mrrosoff/Forager/assets/source_photos/animals/banana_slug.jpg

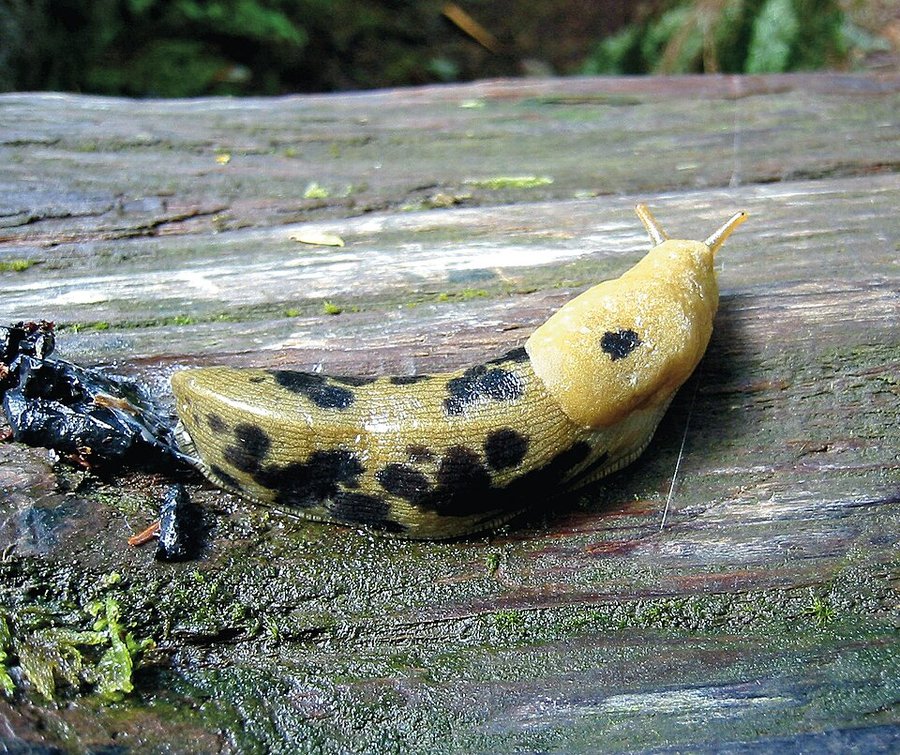
assets/source_photos/animals/banana_slug.jpg
