mrrosoff/Forager/assets/source_photos/animals/barred_owl.jpg

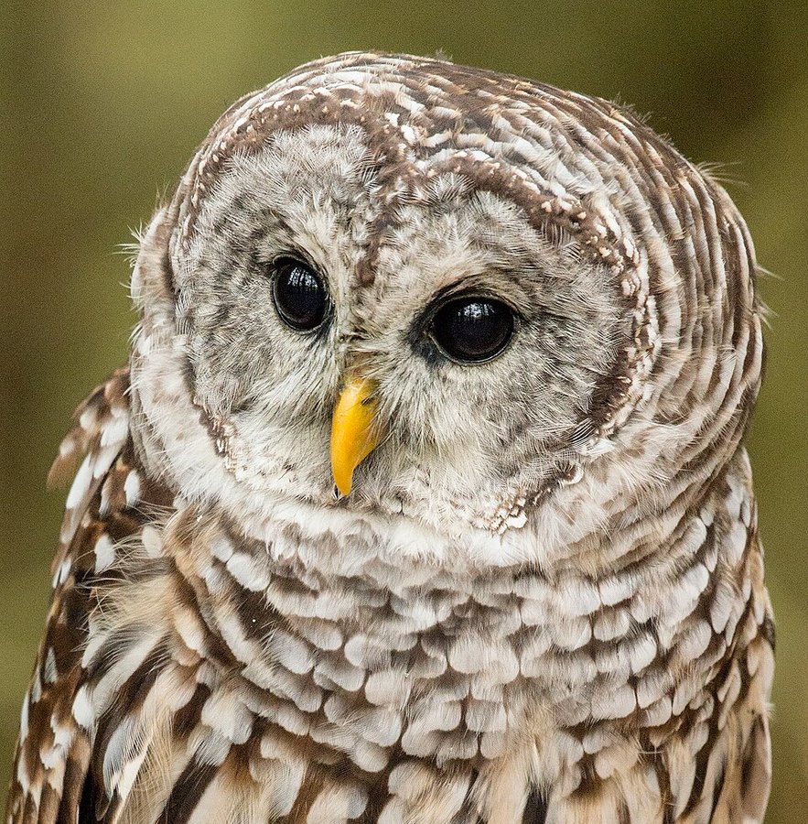
assets/source_photos/animals/barred_owl.jpg
