mrrosoff/Forager/assets/source_photos/animals/beaver.jpg

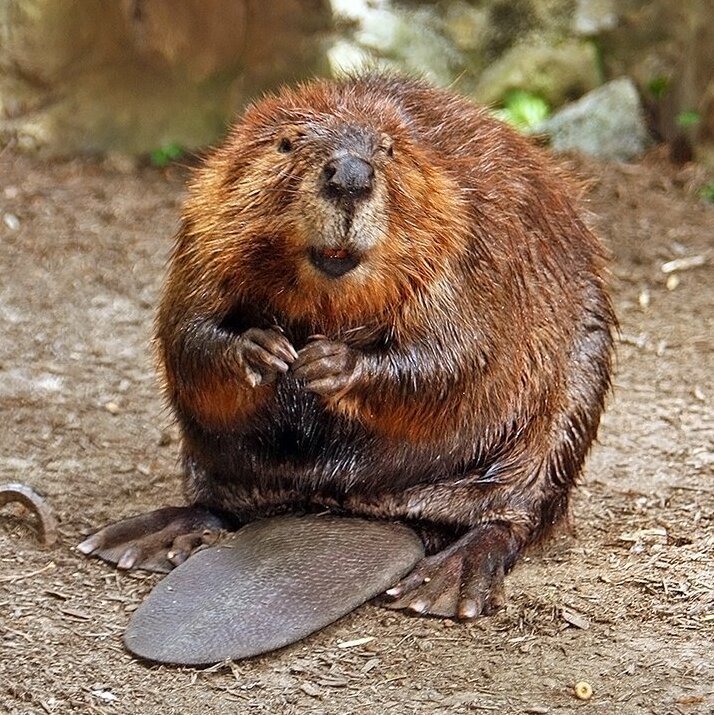
assets/source_photos/animals/beaver.jpg
