mrrosoff/Forager/assets/source_photos/animals/black_bear.jpg

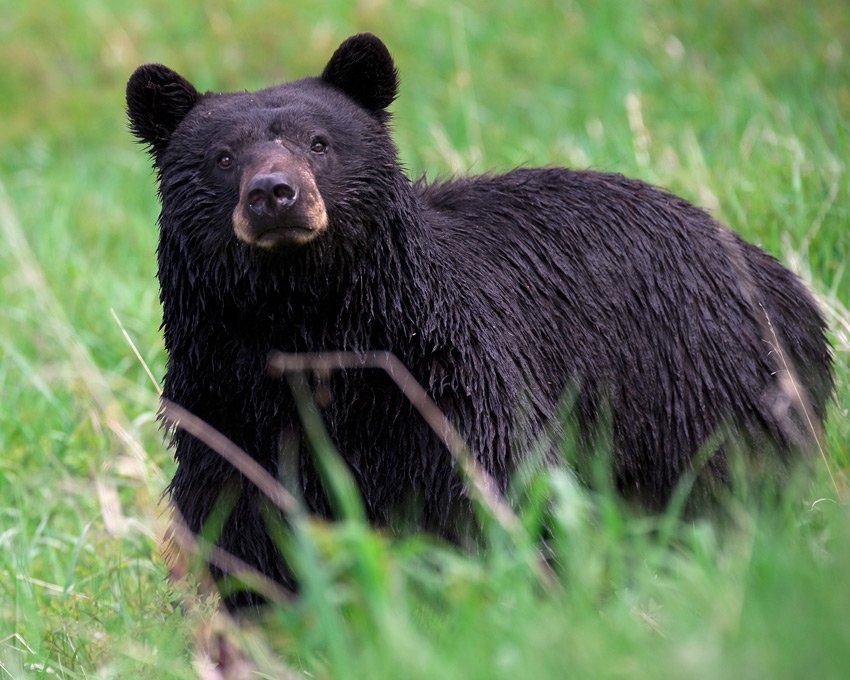
assets/source_photos/animals/black_bear.jpg
