mrrosoff/Forager/assets/source_photos/animals/bobcat.jpg

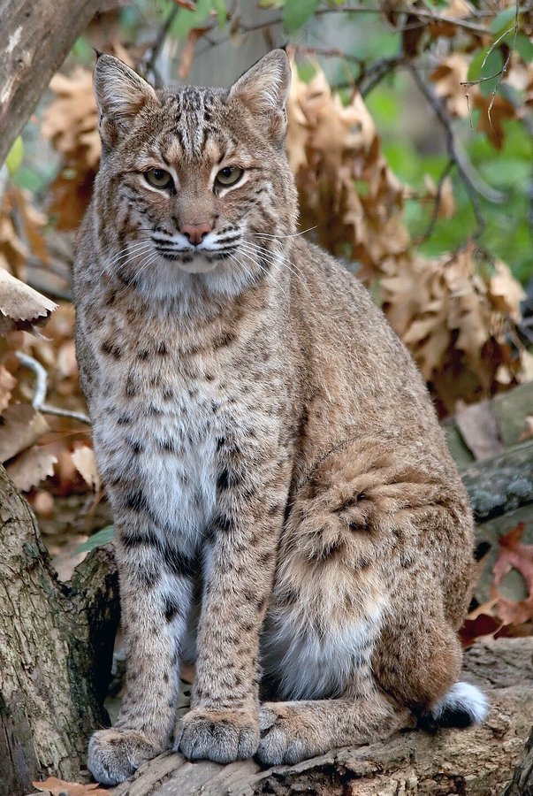
assets/source_photos/animals/bobcat.jpg
