mrrosoff/Forager/assets/source_photos/animals/chickadee.jpg

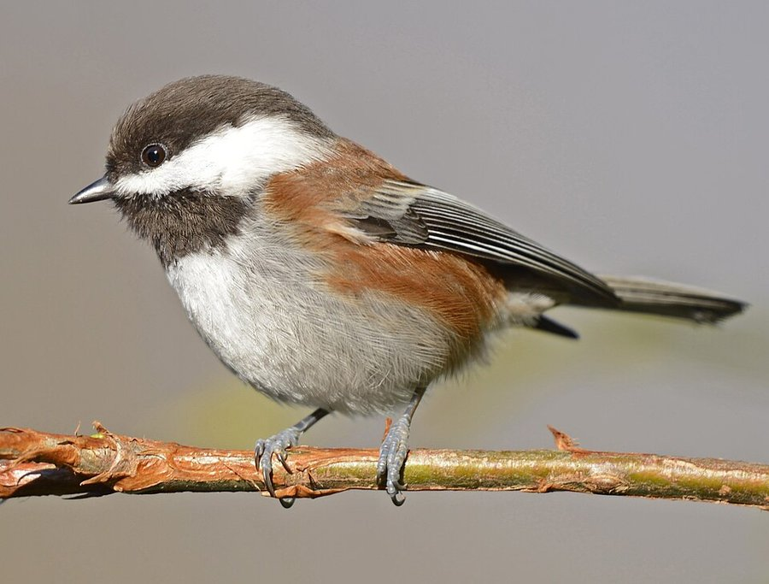
assets/source_photos/animals/chickadee.jpg
