mrrosoff/Forager/assets/source_photos/animals/cougar.jpg

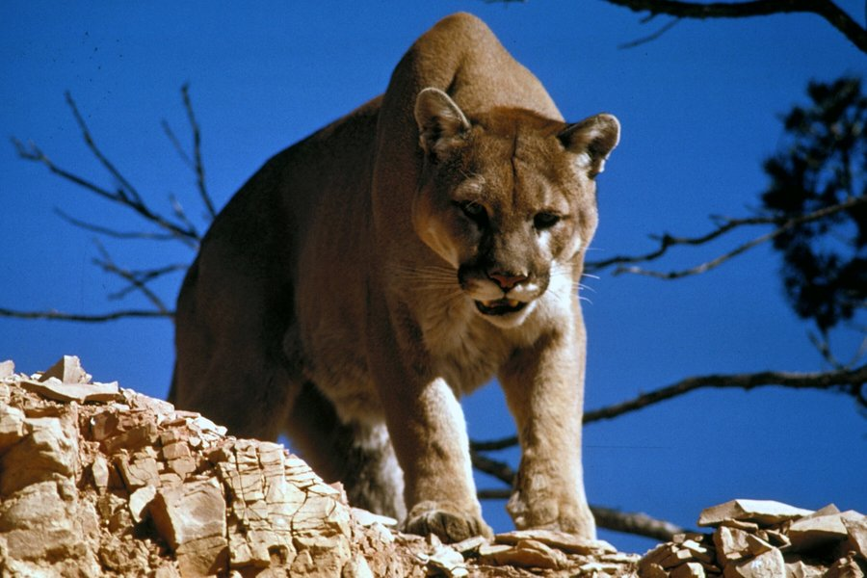
assets/source_photos/animals/cougar.jpg
