mrrosoff/Forager/assets/source_photos/animals/coyote.jpg

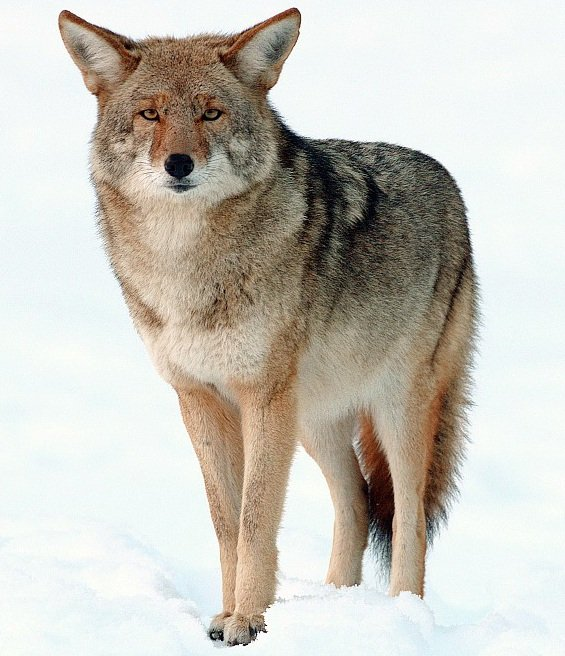
assets/source_photos/animals/coyote.jpg
