mrrosoff/Forager/assets/source_photos/animals/deer.jpg

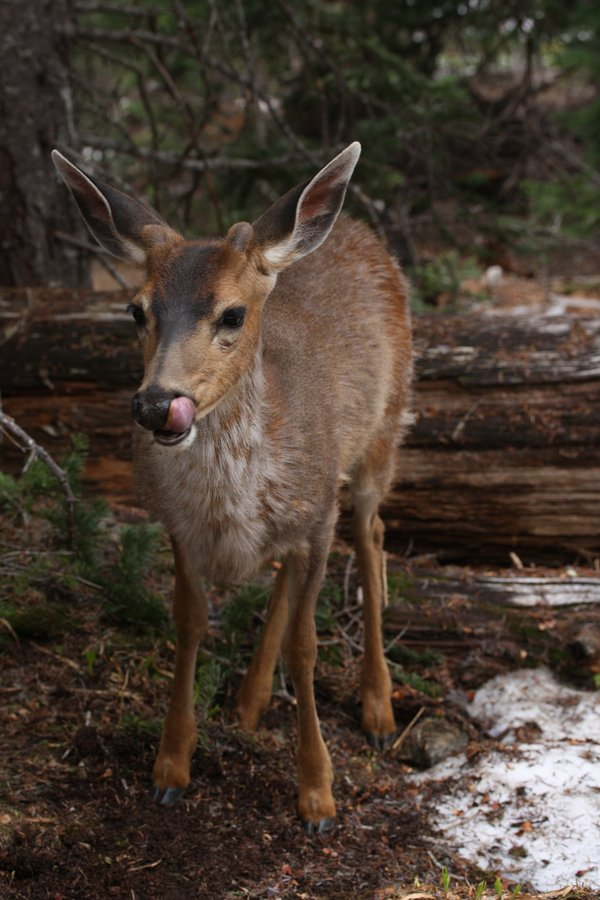
assets/source_photos/animals/deer.jpg
