mrrosoff/Forager/assets/source_photos/animals/elk.jpg

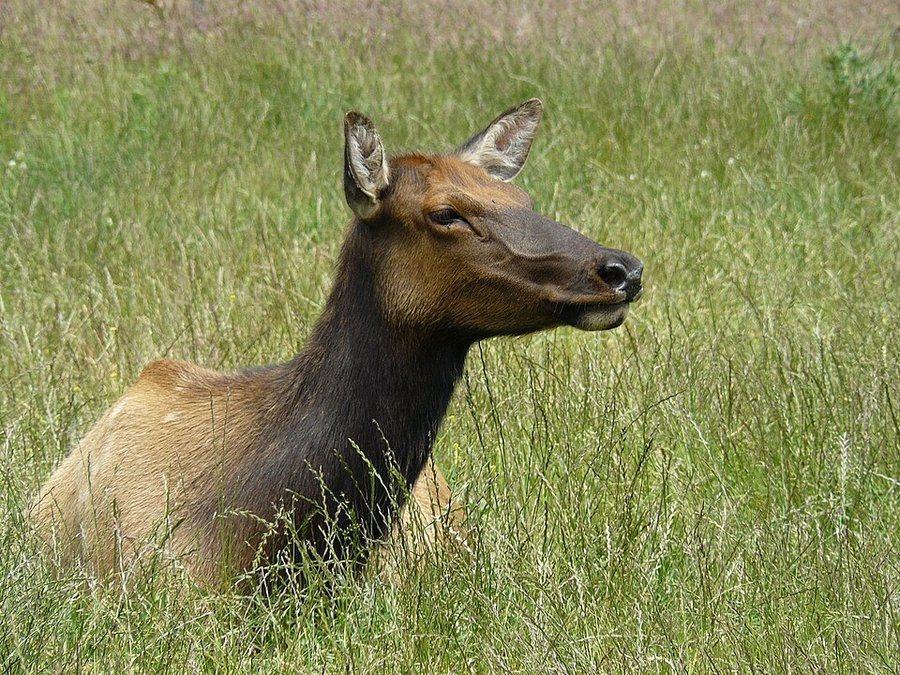
assets/source_photos/animals/elk.jpg
