mrrosoff/Forager/assets/source_photos/animals/gray_wolf.jpg

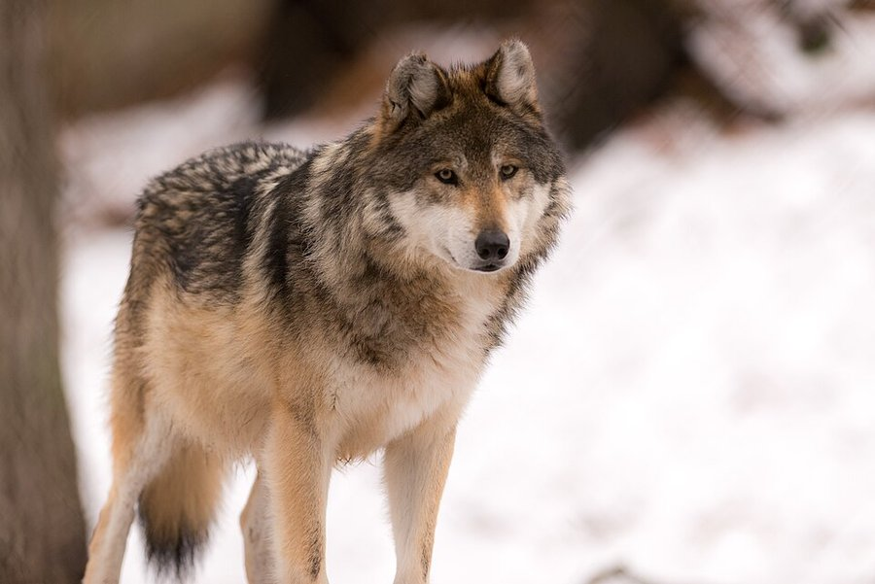
assets/source_photos/animals/gray_wolf.jpg
