mrrosoff/Forager/assets/source_photos/animals/great_blue_heron.jpg

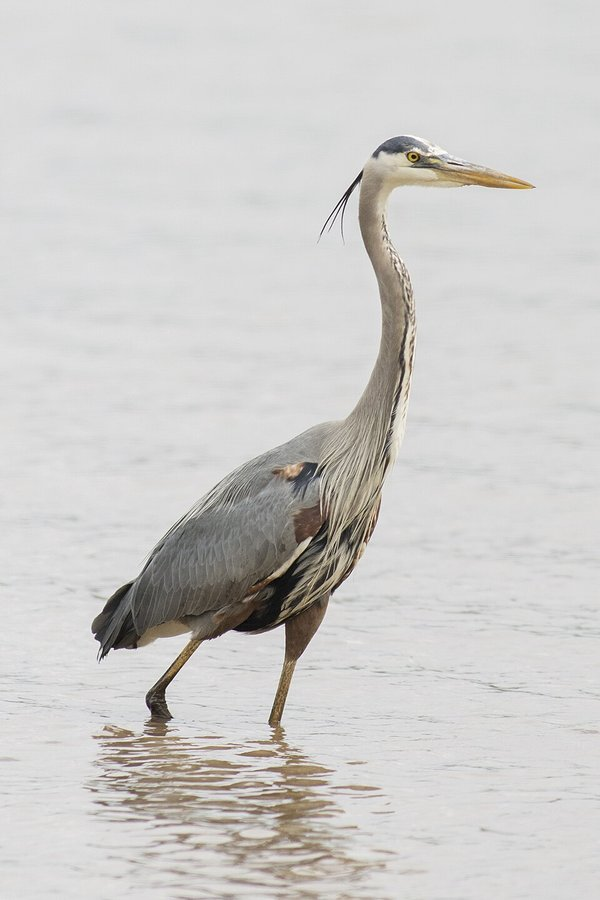
assets/source_photos/animals/great_blue_heron.jpg
