mrrosoff/Forager/assets/source_photos/animals/harbor_seal.jpg

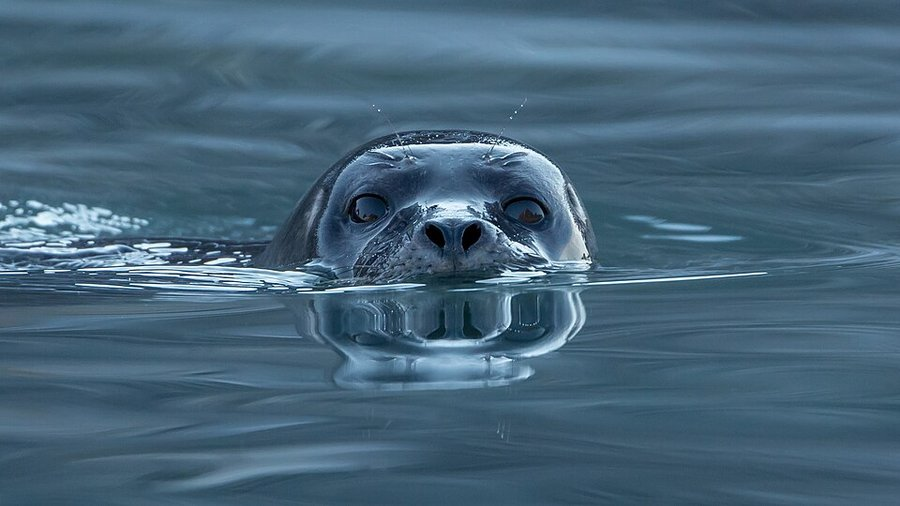
assets/source_photos/animals/harbor_seal.jpg
