mrrosoff/Forager/assets/source_photos/animals/mountain_goat.jpg

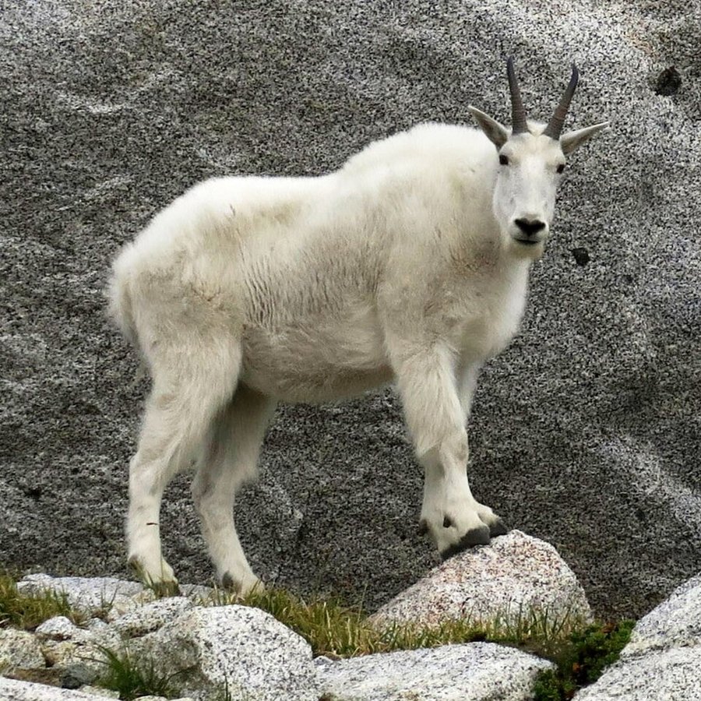
assets/source_photos/animals/mountain_goat.jpg
