mrrosoff/Forager/assets/source_photos/animals/orca.jpg

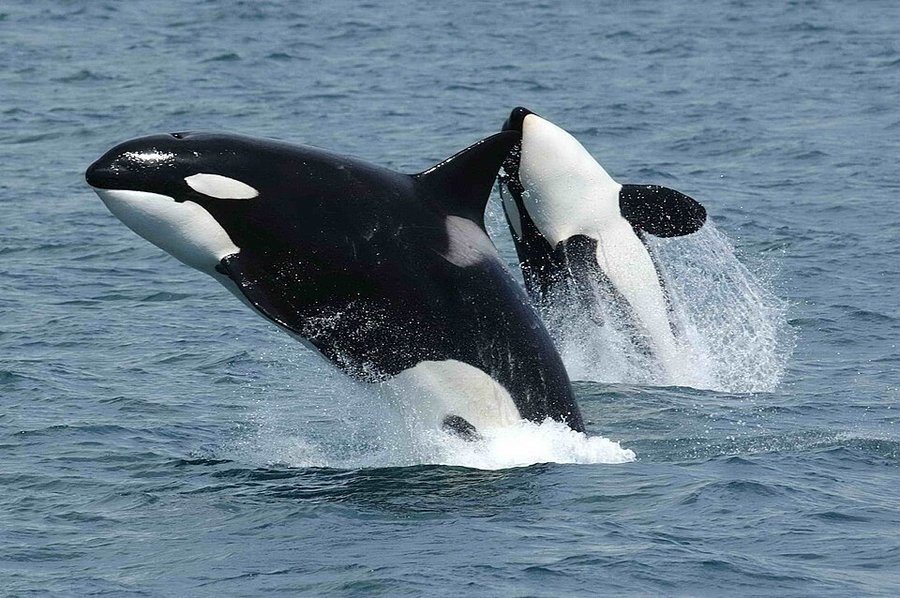
assets/source_photos/animals/orca.jpg
