mrrosoff/Forager/assets/source_photos/animals/osprey.jpg

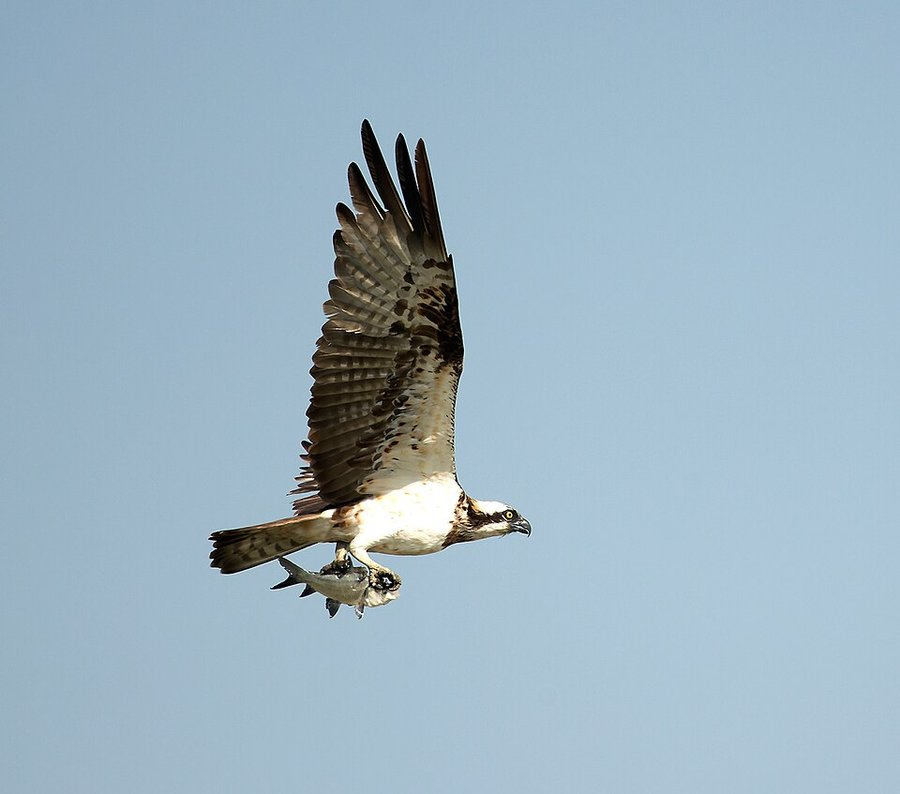
assets/source_photos/animals/osprey.jpg
