mrrosoff/Forager/assets/source_photos/animals/pacific_tree_frog.jpg

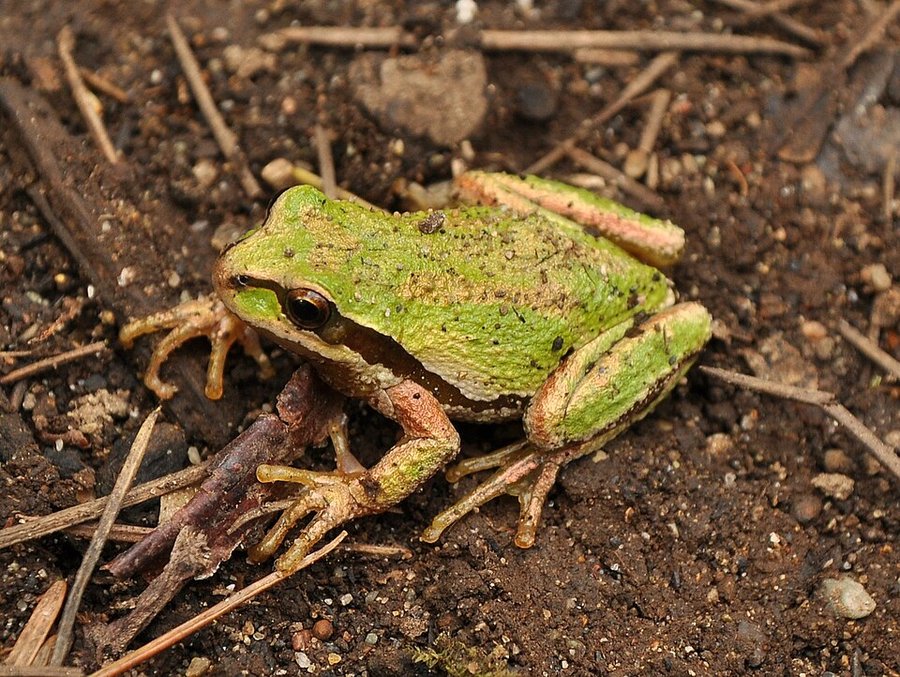
assets/source_photos/animals/pacific_tree_frog.jpg
