mrrosoff/Forager/assets/source_photos/animals/pileated_woodpecker.jpg

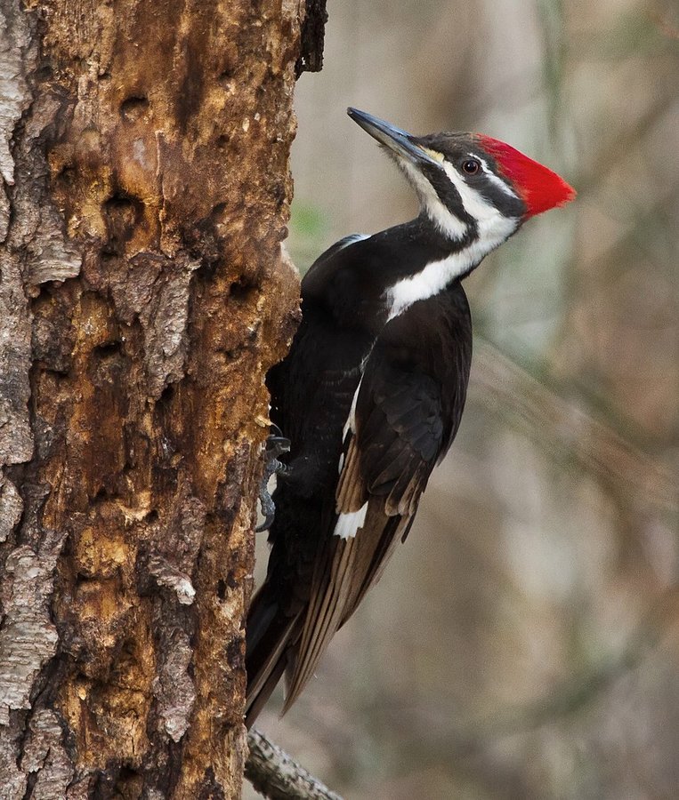
assets/source_photos/animals/pileated_woodpecker.jpg
