mrrosoff/Forager/assets/source_photos/animals/red_fox.jpg

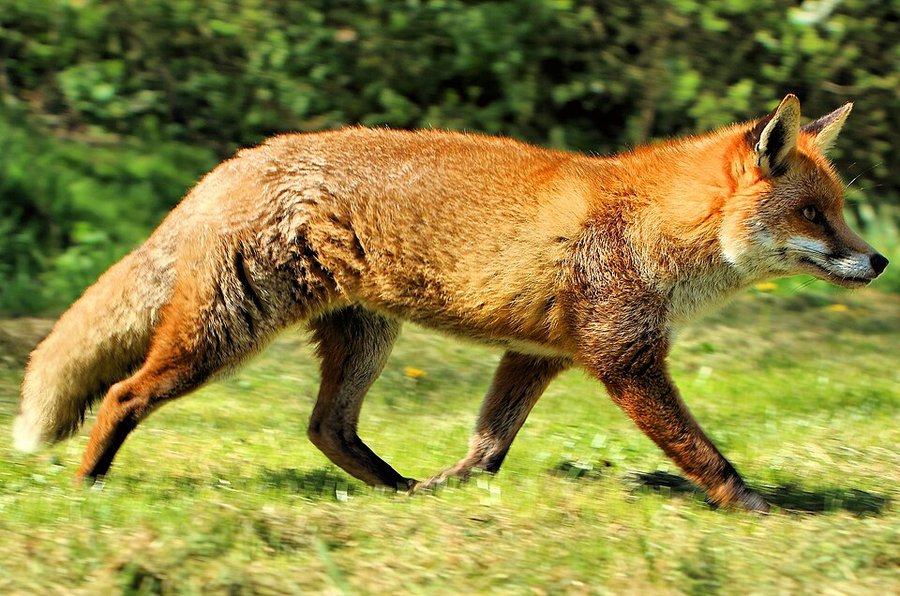
assets/source_photos/animals/red_fox.jpg
