mrrosoff/Forager/assets/source_photos/animals/river_otter.jpg

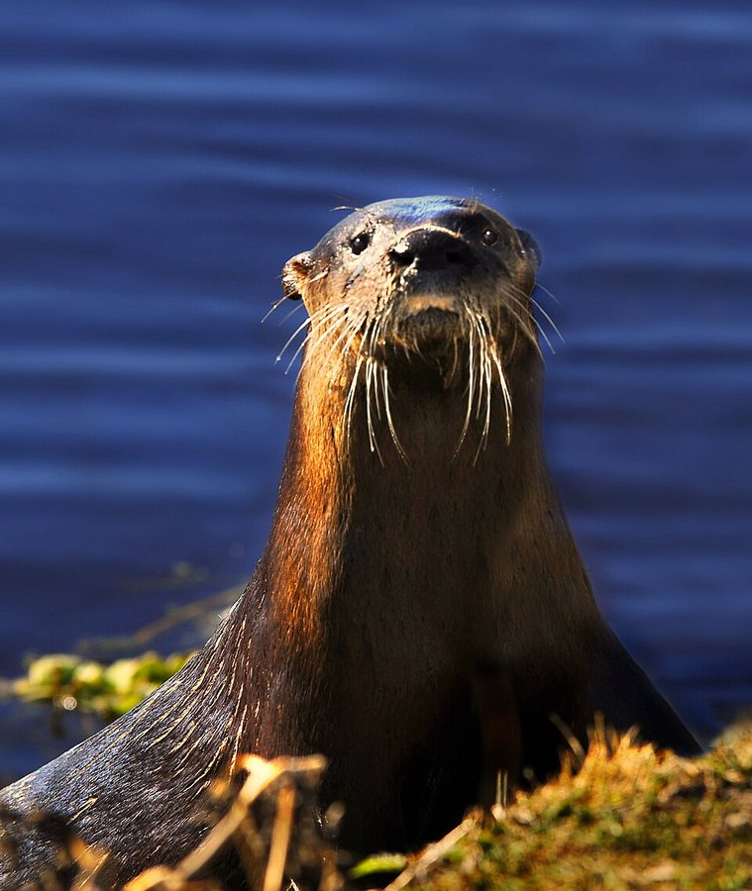
assets/source_photos/animals/river_otter.jpg
