mrrosoff/Forager/assets/source_photos/animals/snowshoe_hare.jpg

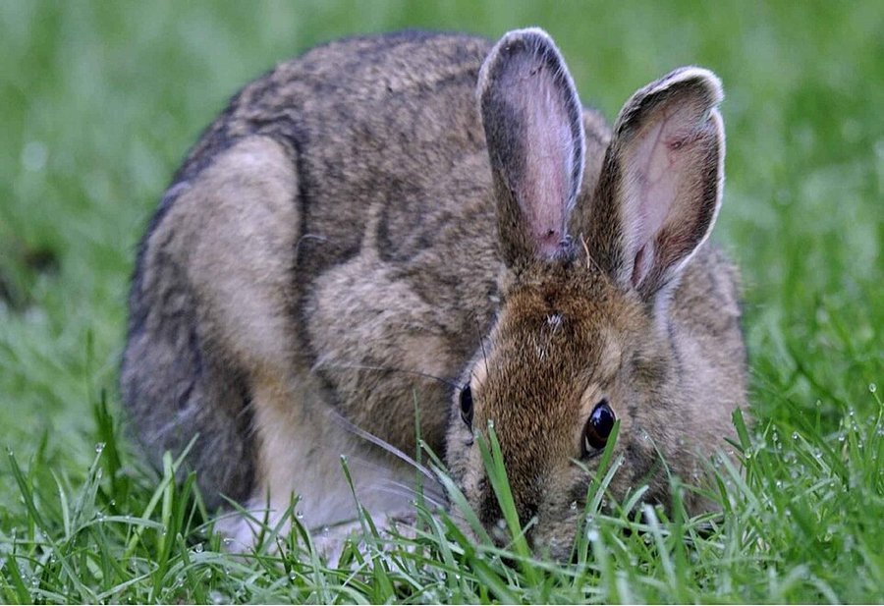
assets/source_photos/animals/snowshoe_hare.jpg
