mrrosoff/Forager/assets/source_photos/animals/stellers_jay.jpg

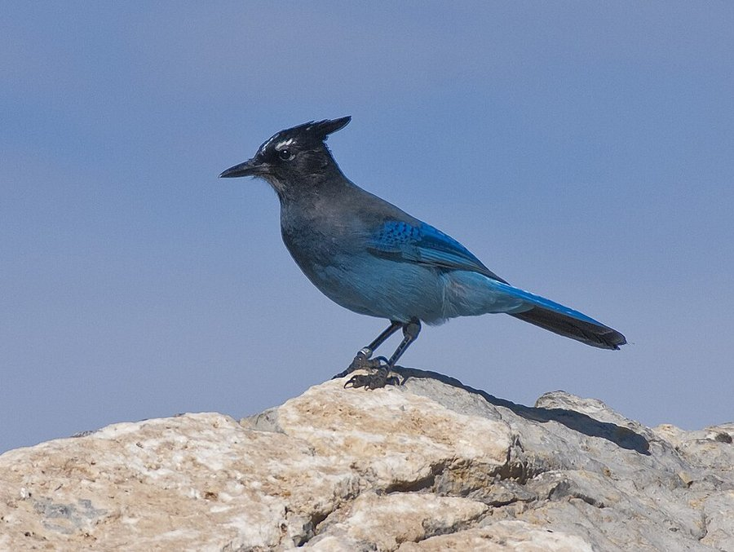
assets/source_photos/animals/stellers_jay.jpg
