mrrosoff/Forager/assets/source_photos/marmot/baby2.jpg

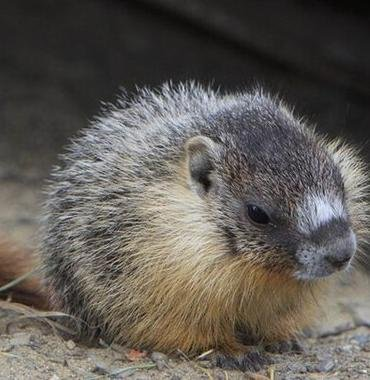
assets/source_photos/marmot/baby2.jpg
