mrrosoff/Forager/assets/source_photos/marmot/baby4.jpg

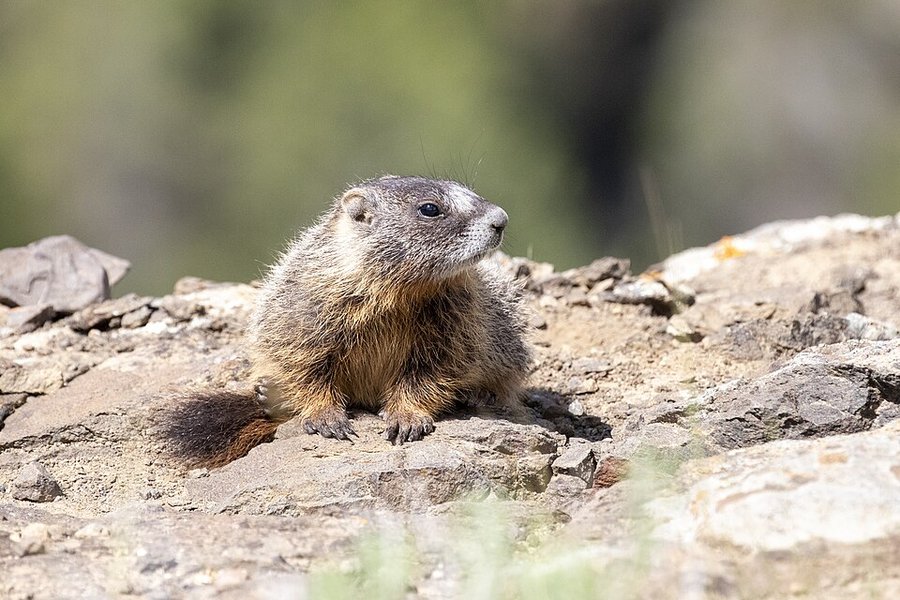
assets/source_photos/marmot/baby4.jpg
