mrrosoff/Forager/assets/source_photos/marmot/baby6.jpg

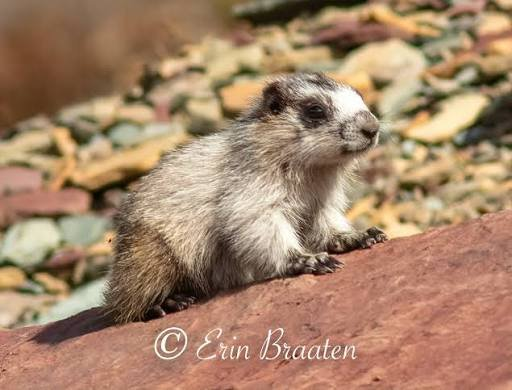
assets/source_photos/marmot/baby6.jpg
