mrrosoff/Forager/assets/source_photos/marmot/baby7.jpg

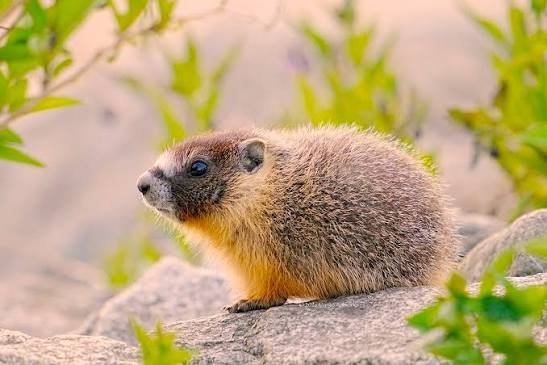
assets/source_photos/marmot/baby7.jpg
