mrrosoff/Forager/assets/source_photos/marmot/baby.jpg

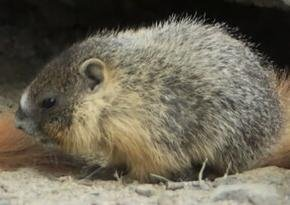
assets/source_photos/marmot/baby.jpg
