mrrosoff/Forager/assets/source_photos/marmot/base.jpg

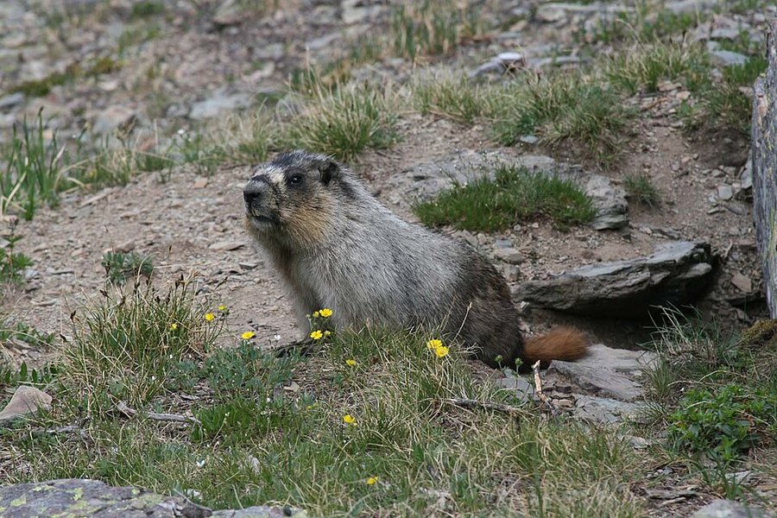
assets/source_photos/marmot/base.jpg
