mrrosoff/Forager/assets/source_photos/marmot/death.jpg

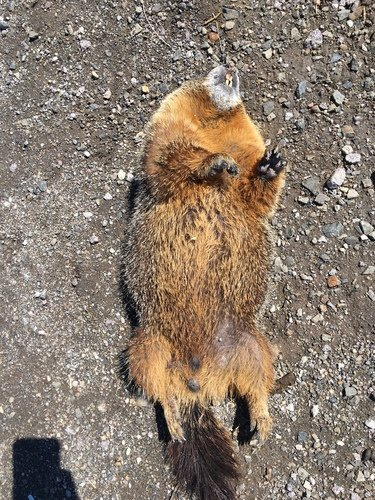
assets/source_photos/marmot/death.jpg
