mrrosoff/Forager/assets/source_photos/marmot/variant5.jpg

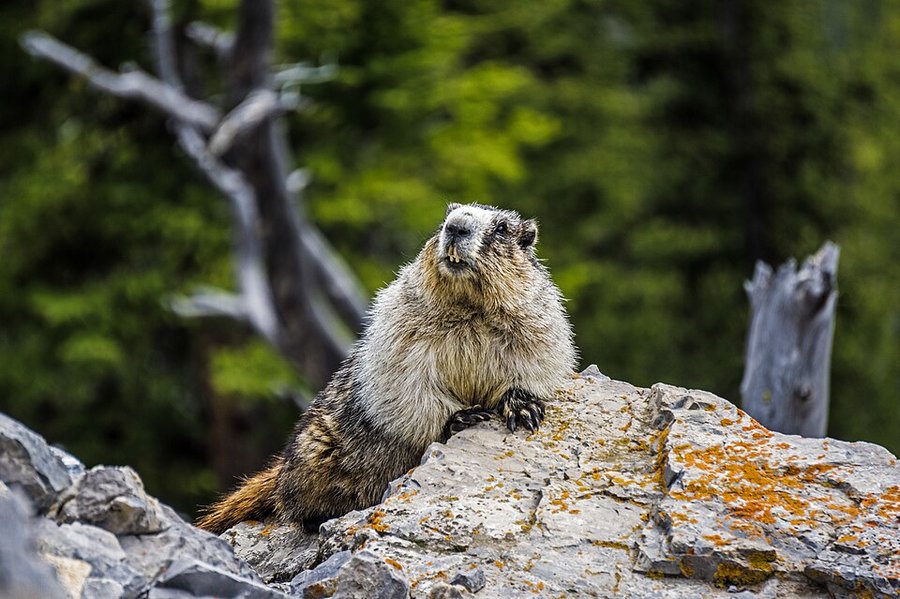
assets/source_photos/marmot/variant5.jpg
