mrrosoff/Forager/assets/source_photos/marmot/variant6.jpg

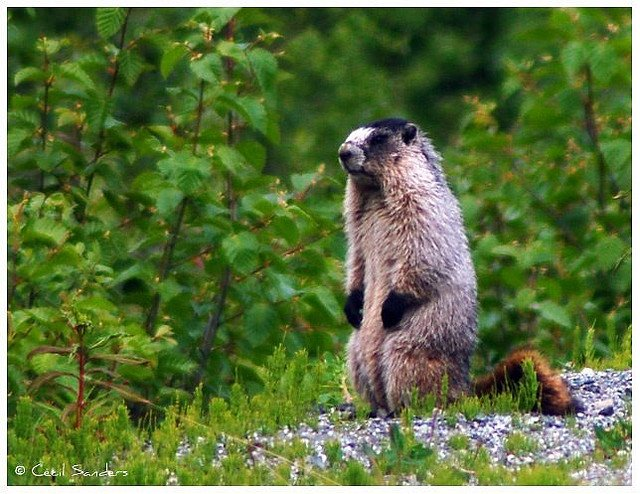
assets/source_photos/marmot/variant6.jpg
