mrrosoff/Forager/assets/source_photos/marmot/variant7.jpg

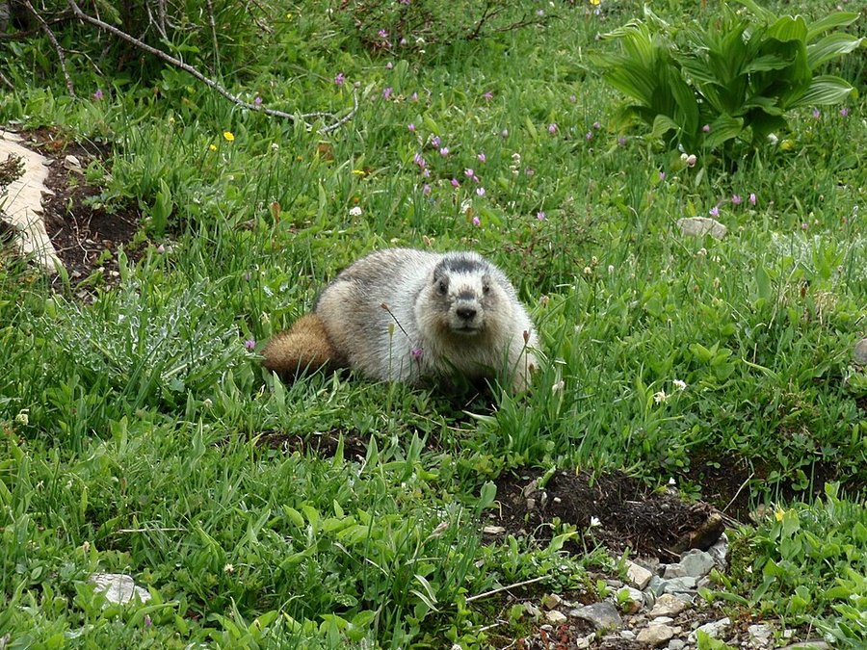
assets/source_photos/marmot/variant7.jpg
