mrrosoff/Forager/assets/source_photos/marmot/variant8.jpg

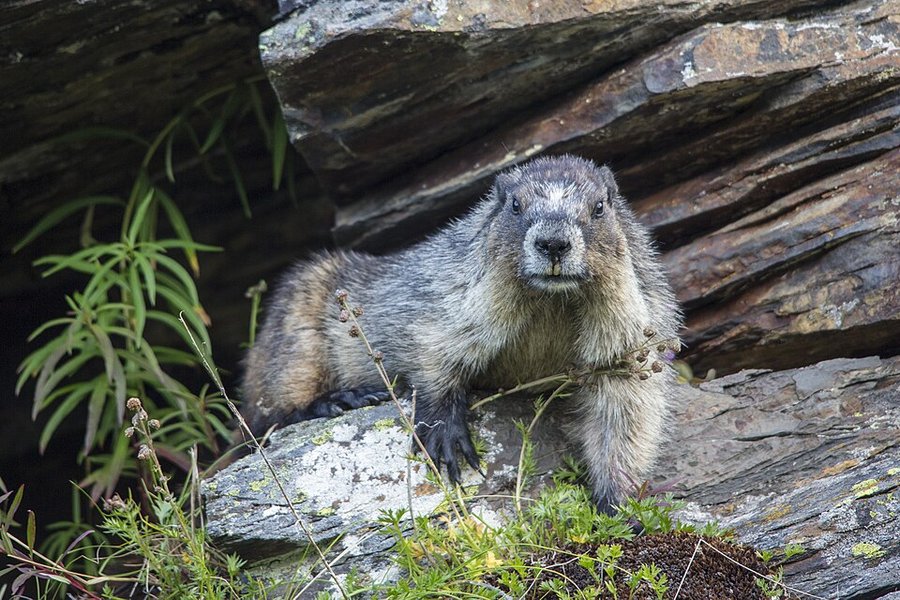
assets/source_photos/marmot/variant8.jpg
