mrrosoff/Forager/assets/source_photos/marmot/variant9.jpg

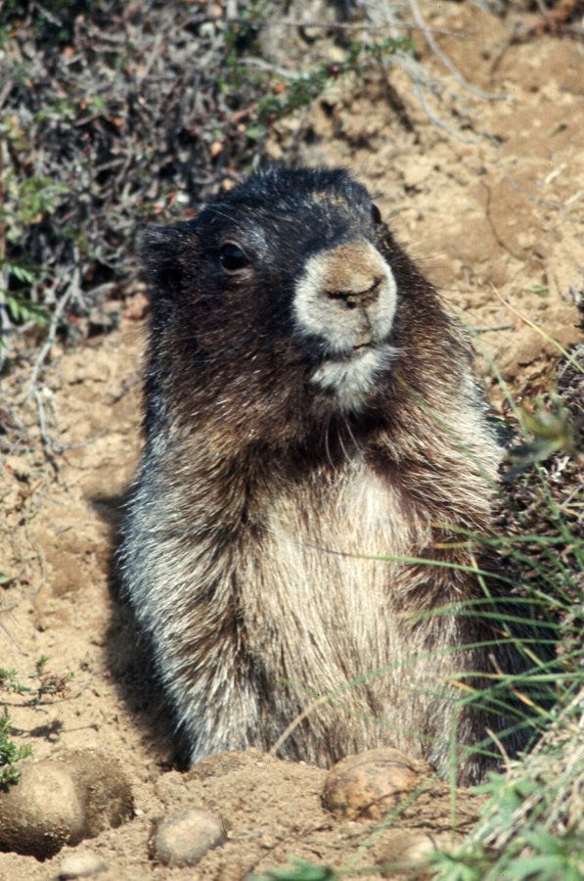
assets/source_photos/marmot/variant9.jpg
