mrrosoff/Forager/assets/source_photos/marmot/variant10.jpg

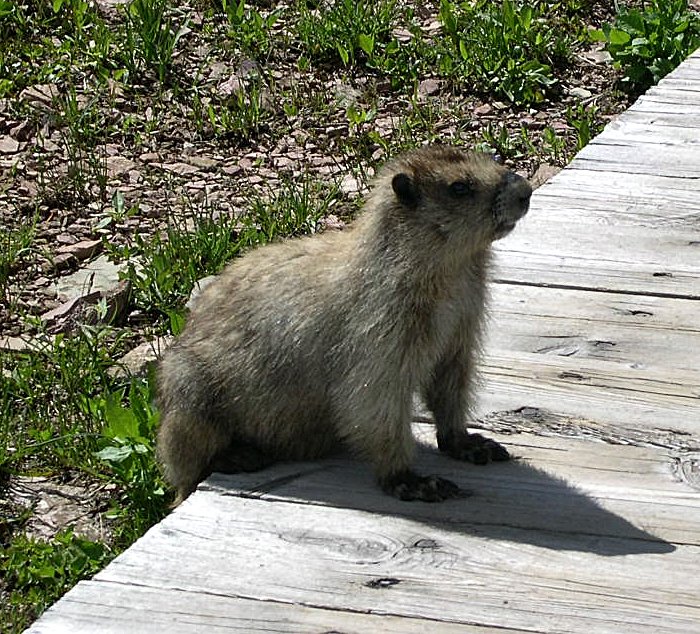
assets/source_photos/marmot/variant10.jpg
