mrrosoff/Forager/assets/source_photos/marmot/variant11.jpg

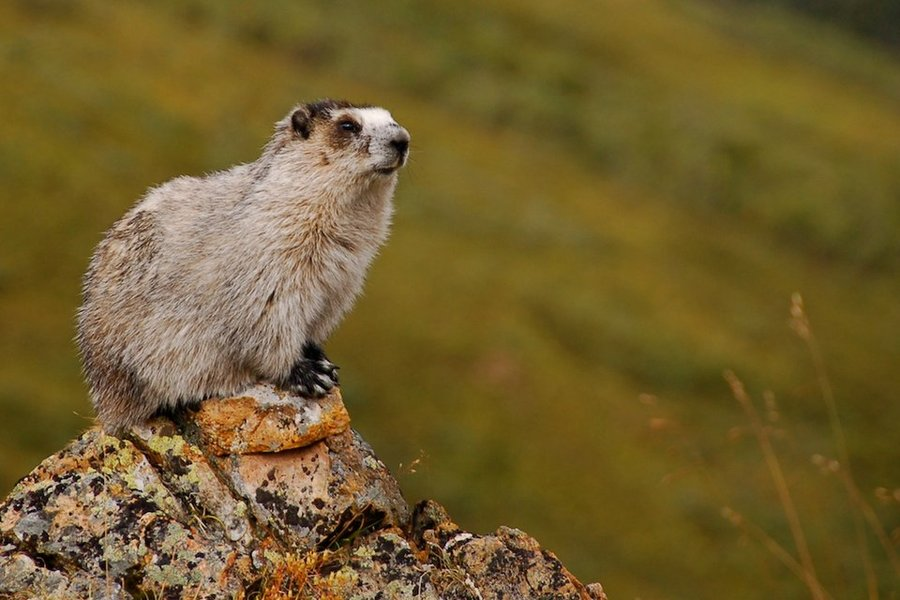
assets/source_photos/marmot/variant11.jpg
