mrrosoff/Forager/assets/source_photos/marmot/variant16.jpg

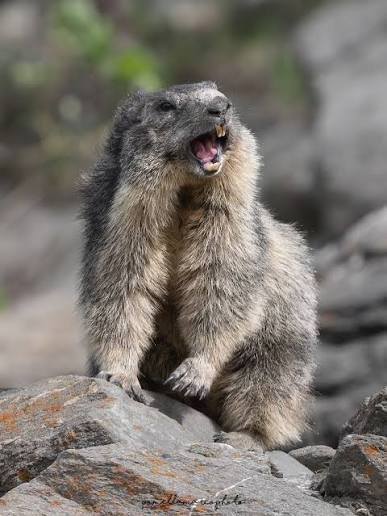
assets/source_photos/marmot/variant16.jpg
