mrrosoff/Forager/assets/source_photos/marmot/variant17.jpg

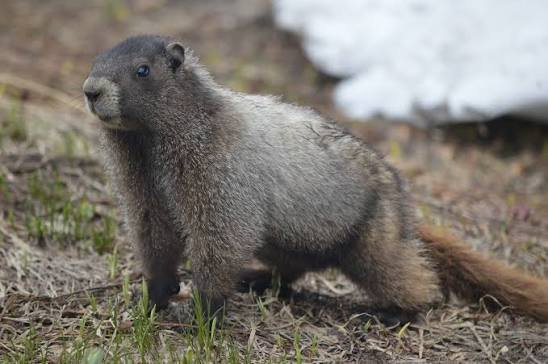
assets/source_photos/marmot/variant17.jpg
