mrrosoff/Forager/assets/source_photos/marmot/variant18.jpg

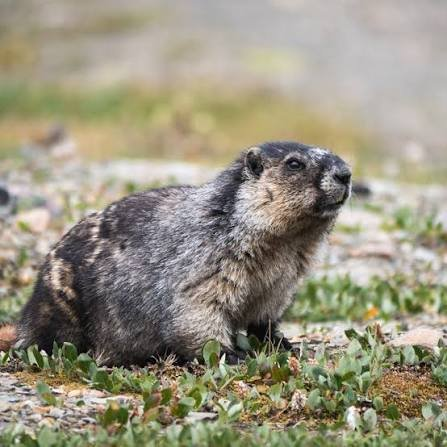
assets/source_photos/marmot/variant18.jpg
