mrrosoff/Forager/assets/source_photos/marmot/variant20.jpg

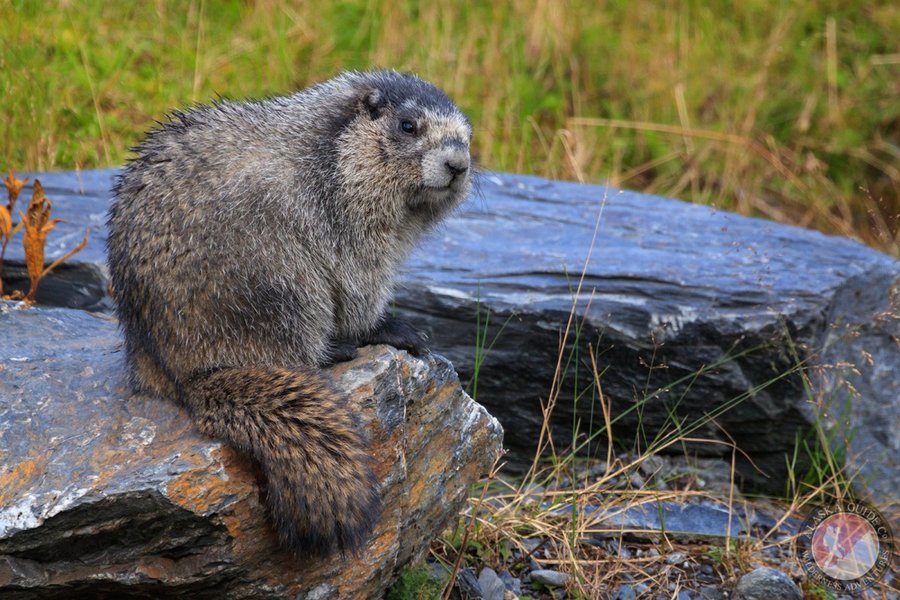
assets/source_photos/marmot/variant20.jpg
