mrrosoff/Forager/assets/source_photos/marmot/variant21.jpg

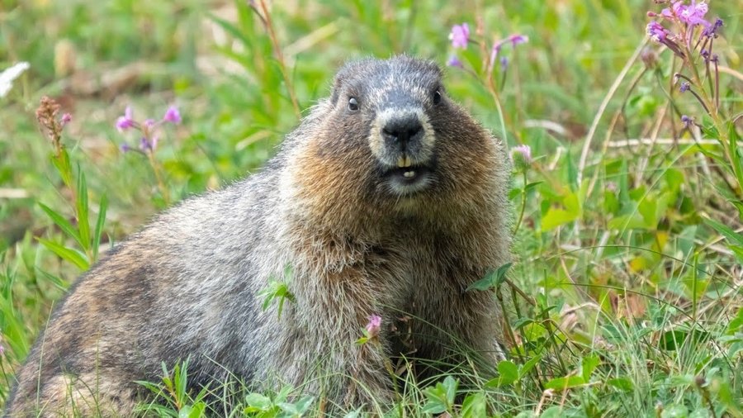
assets/source_photos/marmot/variant21.jpg
