mrrosoff/Forager/assets/source_photos/marmot/variant22.jpg

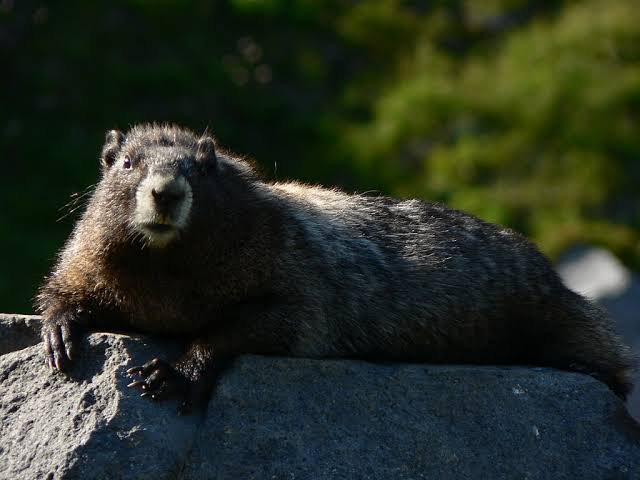
assets/source_photos/marmot/variant22.jpg
