mrrosoff/Forager/assets/source_photos/marmot/variant24.jpg

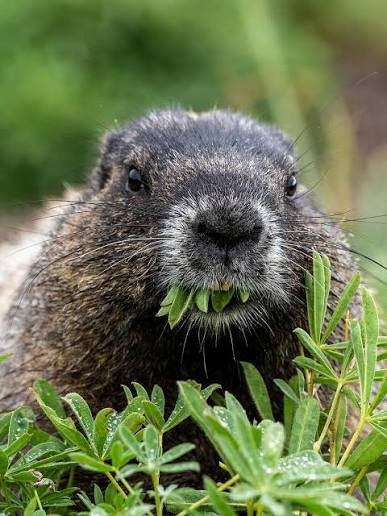
assets/source_photos/marmot/variant24.jpg
