mrrosoff/Forager/assets/source_photos/marmot/variant25.jpg

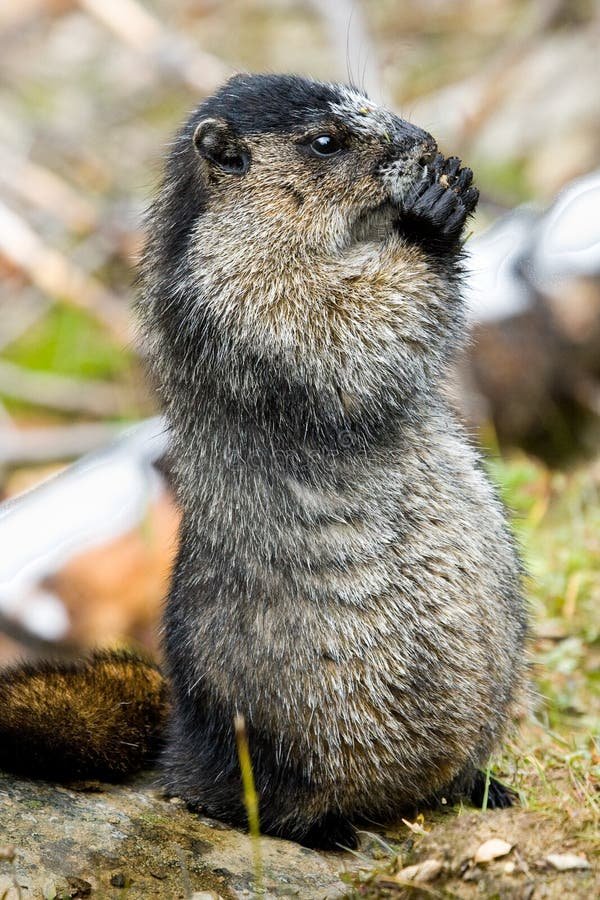
assets/source_photos/marmot/variant25.jpg
