mrrosoff/Forager/assets/source_photos/marmot/variant26.jpg

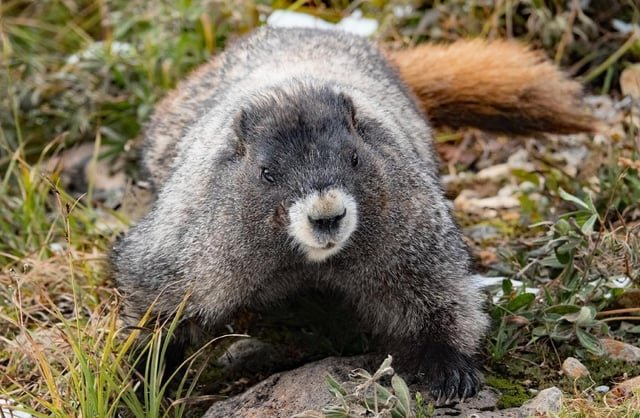
assets/source_photos/marmot/variant26.jpg
