mrrosoff/Forager/assets/source_photos/marmot/variant27.jpg

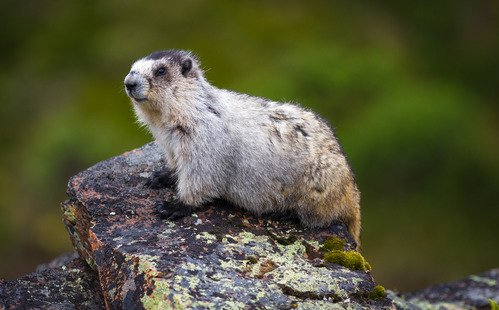
assets/source_photos/marmot/variant27.jpg
