mrrosoff/Forager/assets/source_photos/marmot/variant28.jpg

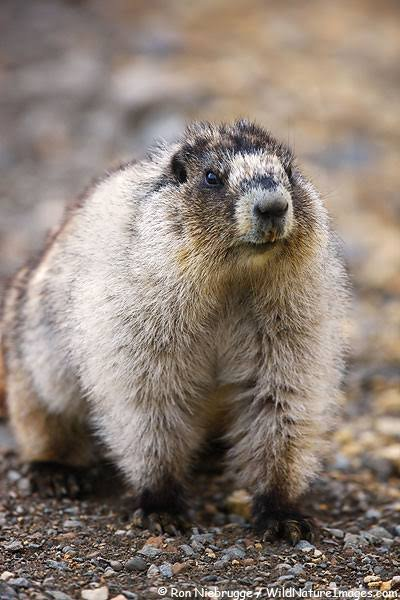
assets/source_photos/marmot/variant28.jpg
