mrrosoff/Forager/enclosure/preview/01_bezel_front.png

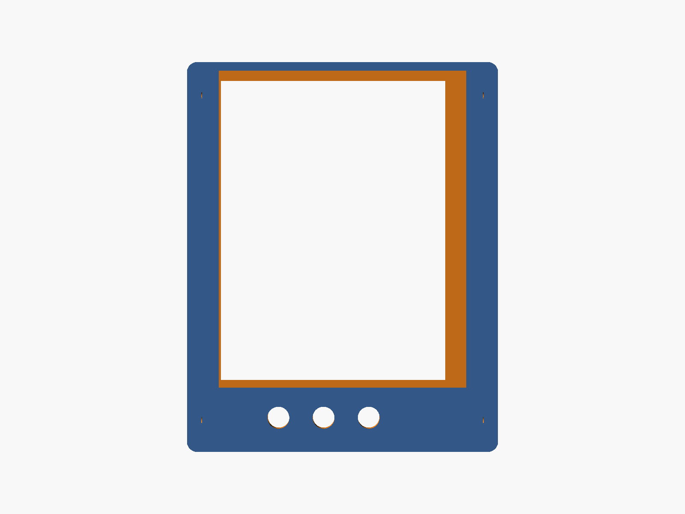
enclosure/preview/01_bezel_front.png
