mrrosoff/Forager/enclosure/preview/02_bezel_iso.png

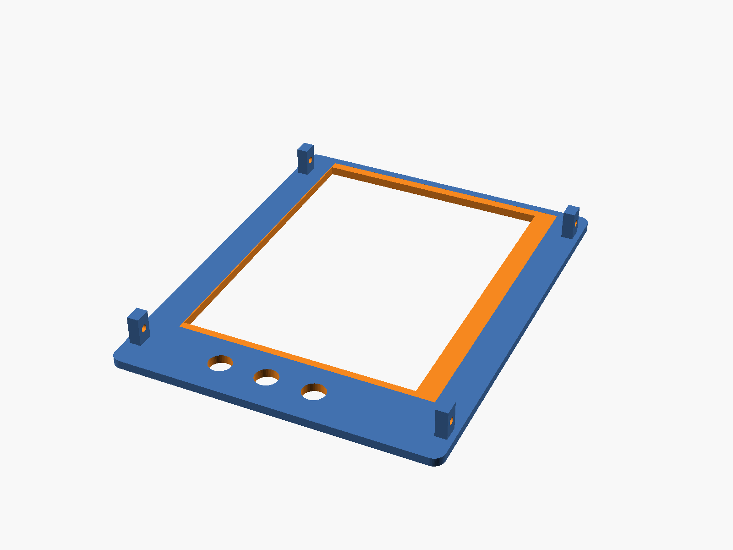
enclosure/preview/02_bezel_iso.png
