mrrosoff/Forager/enclosure/preview/03_tray_interior.png

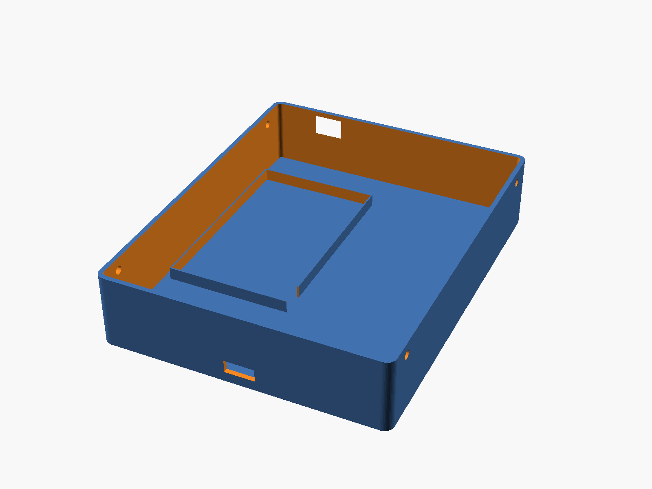
enclosure/preview/03_tray_interior.png
