mrrosoff/Forager/enclosure/preview/04_tray_exterior.png

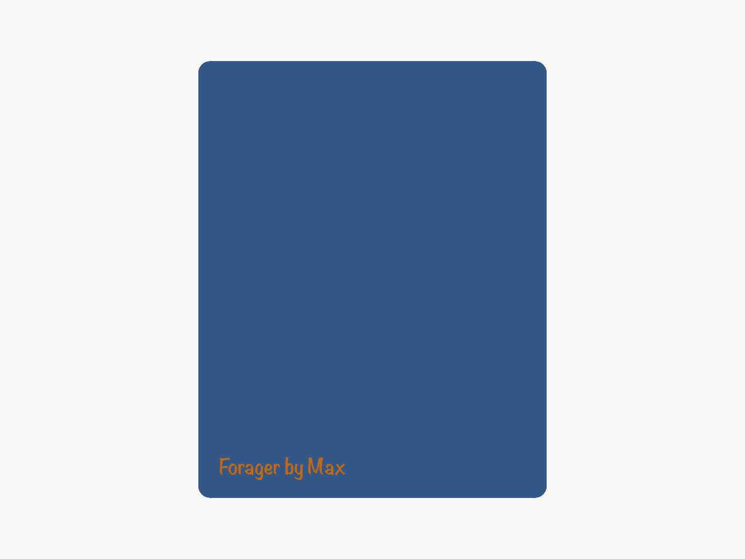
enclosure/preview/04_tray_exterior.png
