mrrosoff/Forager/enclosure/preview/05_assembled_overview.png

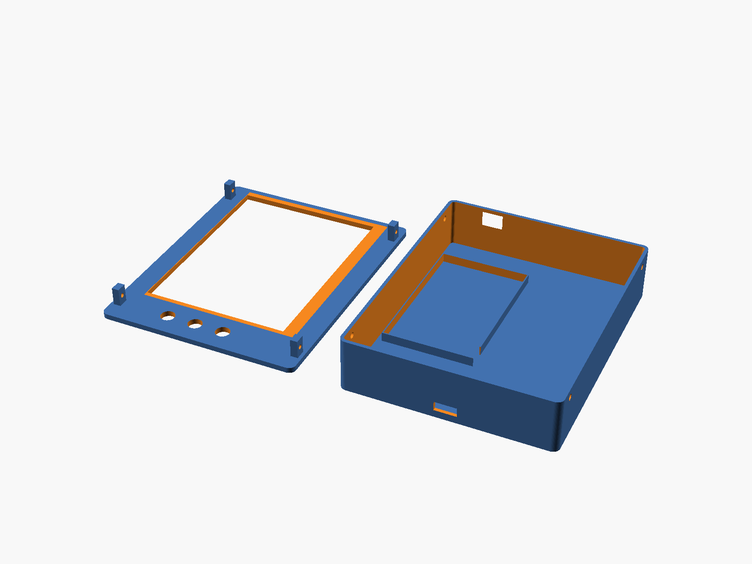
enclosure/preview/05_assembled_overview.png
