mrrosoff/Forager/src/foraging/foraging_species.h

// foraging_species.h — the master PNW/Seattle foraging reference table.
// Pure data, split out of foraging.cpp so that file is mostly logic. Only
// included from foraging.cpp, which #defines the MO(month) bitmask macro
// used throughout before including this.
#pragma once

#include "model.h"

// monthMask bits mark active months (1=Jan .. 12=Dec, via the MO() macro).
// caution is "" when there's no meaningful look-alike risk.
static const Forageable kSpecies[] = {
    {"Dead Man's Fingers", "mushroom", "Dark charcoal-black finger-like clubs pushing up from buried wood.",
     "Not edible -- tough and bitter, just a striking find.",
     "Look for the dark clustered fingers at the base of rotting stumps.", MO(6) | MO(7) | MO(8),
     Biome::Forest},

    {"Miner's Lettuce", "green", "Round leaf cupping the stem. Shady wet banks.", "",
     "Snip above the root so the patch regrows.", MO(1) | MO(2) | MO(3), Biome::Forest},

    {"Stinging Nettle", "green", "First tips now. Gloves on; cooking kills the sting.",
     "Wear gloves -- fresh leaves sting on contact.",
     "Pick only the top 4-6 leaves per plant, gloved.", MO(2) | MO(3) | MO(4), Biome::Forest},

    {"Oyster Mushroom", "mushroom", "Shelving on dead alder and maple after rain.",
     "Check for the Angel Wing lookalike on conifers -- avoid it.",
     "Cut at the base of the cluster, leave small ones.", MO(1) | MO(2) | MO(11) | MO(12),
     Biome::Forest},

    {"Morel", "mushroom", "Honeycomb cap. Watch cottonwoods as soil warms.",
     "True morels are hollow top to bottom -- cut one to confirm.",
     "Check burn sites and cottonwood river bottoms.", MO(3) | MO(4), Biome::Forest},

    {"Chickweed", "green", "Tender mats in disturbed ground. Mild, fresh.", "",
     "Best before flowering; snip the top few inches.", MO(3) | MO(4) | MO(5), Biome::Forest},

    {"Ramps", "green", "Wild leek. Harvest one leaf, leave the bulb.", "",
     "Take a single leaf per plant so the patch survives.", MO(4), Biome::Forest},

    {"Fiddlehead Fern", "green", "Tight coils of lady fern. Pick before they unfurl.",
     "Must be cooked thoroughly; avoid bracken fern lookalikes.",
     "Snap coils that are still tightly curled, under 2 inches.", MO(4) | MO(5), Biome::Forest},

    {"Elderflower", "flower", "Creamy umbels. Cordial weather. Never the leaves.",
     "Leaves and stems are toxic -- flowers and ripe berries only.",
     "Cut whole flower clusters, shake off insects first.", MO(5) | MO(6), Biome::Forest},

    {"Wood Sorrel", "green", "Shamrock leaf, lemony bite. Forest floor and trailside.",
     "High in oxalic acid -- a trailside nibble, not a meal.",
     "Pinch leaves and stems; avoid roadside patches.", MO(5) | MO(6) | MO(7), Biome::Forest},

    {"Salmonberry", "berry", "Earliest berry. Golden to red, along streams.", "",
     "Ripe berries pull free easily; unripe ones resist.", MO(6), Biome::Forest},

    {"Chanterelle", "mushroom", "Apricot scent, false gills. Conifer duff after warm rain.",
     "False ridges, not true blades -- a key ID feature vs toxic lookalikes.",
     "Look on slopes under Douglas fir a week after rain.", MO(7) | MO(8) | MO(9), Biome::Forest},

    {"Blackberry", "berry", "Himalayan brambles everywhere. Sun-warmed edges.", "",
     "Sun-facing berries ripen first; watch for thorns.", MO(8) | MO(9), Biome::Forest},

    {"Matsutake", "mushroom", "Spicy-cinnamon pine mushroom. Sandy conifer soil.", "",
     "Look for cracked duff mounds near pine roots.", MO(9), Biome::Forest},

    {"Lobster Mushroom", "mushroom", "Orange parasitized host. Firm, seafood-sweet.",
     "The host mushroom underneath is irrelevant once parasitized.",
     "Firm all the way through means it's good to eat.", MO(9) | MO(10), Biome::Forest},

    {"Porcini", "mushroom", "King bolete. Fat white stem, no gills -- pores instead.",
     "Check for pores, not gills; avoid soft or wormy caps.",
     "Firm caps only; check the stem base for grubs.", MO(10), Biome::Forest},

    {"Yellowfoot", "mushroom", "Winter chanterelle. Hollow stem, late and cold-hardy.", "",
     "Keeps fruiting through light frost -- check familiar patches.", MO(11) | MO(12),
     Biome::Forest},

    {"Velvet Shank", "mushroom", "Enokitake's wild cousin. Orange caps in cold snaps.",
     "Sticky cap and velvety stem distinguish it from toxic Galerina.",
     "Fruits on hardwood stumps during cold snaps.", MO(12) | MO(1), Biome::Forest},

    {"Huckleberry", "berry", "Subalpine slopes. Ripens as you gain elevation.", "",
     "Higher elevation = later ripening; chase the season uphill.", MO(7) | MO(8), Biome::Mountain},

    {"Raspberry", "berry", "Wild cane fruit at forest edges and old clearings.", "",
     "Tug ripe berries gently -- they pull free of the core when ready.", MO(7) | MO(8),
     Biome::Mountain},

    {"Mountain Cranberry", "berry", "Lingonberry cousin. Tart red berries in dwarf mats.", "",
     "Best after light frost sweetens the fruit; pick sparingly.", MO(9) | MO(10), Biome::Mountain},

    {"Devil's Club Shoots", "green", "Spring shoots, mild and green before the spines toughen.",
     "Cook thoroughly; handle mature stalks with gloves -- spiny.",
     "Snap shoots while still tender, before leaves fully open.", MO(4) | MO(5), Biome::Mountain},

    {"Swamp Onion", "green", "Wild mountain onion in wet subalpine meadows.", "",
     "Pull gently from soft mud; rinse the bulb at the creek.", MO(6) | MO(7), Biome::Mountain},

    {"Douglas Fir Tips", "flower", "Bright citrus-pine new growth at branch ends.",
     "Don't confuse with Pacific yew -- yew needles are toxic.",
     "Pinch only the pale new candle growth, not old needles.", MO(4) | MO(5), Biome::Mountain},

    {"Bull Kelp", "seaweed", "Long whip stipe with a bulb float; drifts up after storms.",
     "Harvest drift only, or cut blade above the holdfast to regrow.",
     "Gather fresh drift kelp on the tideline after a blow.", MO(6) | MO(7) | MO(8) | MO(9),
     Biome::Coast},

    {"Sugar Kelp", "seaweed", "Wavy golden-brown blade in the low intertidal.", "",
     "Cut blades an inch above the holdfast at a minus tide.", MO(5) | MO(6) | MO(7), Biome::Coast},

    {"Sea Lettuce", "seaweed", "Bright green, tissue-thin sheets on mid-tide rocks.",
     "Rinse well -- can harbor grit and small amphipods.",
     "Pick loose, undamaged sheets; avoid ones near outfalls.", MO(4) | MO(5) | MO(6) | MO(7),
     Biome::Coast},

    {"Ochre Sea Star", "shellfish", "Chunky five-armed sea star in orange or deep purple, gripping rocks.",
     "Not edible -- a tidepool sight, not a snack.",
     "Look on rocky shores at low tide, often in tight clusters.", MO(6) | MO(7) | MO(8),
     Biome::Coast},

    {"Sea Asparagus", "green", "Pickleweed. Crunchy, salty segmented stems in the marsh.", "",
     "Snip the top two joints only, leave the rooted base.", MO(6) | MO(7) | MO(8) | MO(9),
     Biome::Coast},

    {"Goosetongue", "green", "Sea plantain. Fleshy, briny blades on the upper beach.", "",
     "Pick young center leaves; avoid grazed or muddy patches.", MO(5) | MO(6) | MO(7),
     Biome::Coast},

    {"Silverweed", "green", "Silvery-leaved runner in upper tidal meadows.", "",
     "Dig slender roots in fall after the leaves die back.", MO(9) | MO(10), Biome::Coast},

    {"Beach Strawberry", "berry", "Low dune mats, small intensely sweet fruit.", "",
     "Search sandy, sun-facing dune grass for ripe red fruit.", MO(7) | MO(8), Biome::Coast},

    {"Beach Pea", "flower", "Purple-pink pea flowers along driftwood lines.",
     "Raw seeds are mildly toxic in quantity -- young pods only, cooked.",
     "Pick flat young pods before the seeds swell and harden.", MO(6) | MO(7) | MO(8),
     Biome::Coast},

    {"Wild Rose Hips", "berry", "Bright orange-red hips on beach and hedgerow roses.",
     "Scrape out the irritating seed hairs before eating.",
     "Pick after the first frost sweetens the hip.", MO(9) | MO(10), Biome::Coast},

    {"Razor Clam", "shellfish", "Fast-digging bivalve on open sand surf beaches.",
     "Check state biotoxin/PSP closures and hold a license before digging.",
     "Look for a 'show' dimple in the sand, then dig fast.",
     MO(10) | MO(11) | MO(12) | MO(1) | MO(2) | MO(3), Biome::Coast},

    {"Shaggy Mane", "mushroom", "Tall shaggy cap, self-digests to ink within hours.",
     "Do not pair with alcohol -- some report Coprine-like reactions; eat fresh only.",
     "Pick young, still-white caps in lawns and disturbed soil.", MO(9) | MO(10) | MO(11),
     Biome::Forest},

    {"Death Cap", "mushroom", "Deadly amanita. White gills, skirt ring, sac at base.",
     "Deadly poisonous -- responsible for most fatal mushroom poisonings; know it to avoid it, "
     "never eat.",
     "Do not harvest -- learn to spot the white gills and basal cup under oaks and ornamentals.",
     MO(9) | MO(10) | MO(11), Biome::Forest},

    {"Destroying Angel", "mushroom", "Pure white amanita with a sac at the base.",
     "Deadly poisonous -- pure white all over is a red flag, not a green light; never eat.",
     "Do not harvest -- if you dig one up for ID, check for the volva sac at the buried base.",
     MO(9) | MO(10) | MO(11), Biome::Forest},

    {"Fly Agaric", "mushroom", "Iconic red cap with white warts, under birch and pine.",
     "Toxic and psychoactive -- causes serious GI distress and neurotoxic effects; not a food.",
     "Admire, don't pick -- easy to ID by the red cap and white flecks.", MO(9) | MO(10) | MO(11),
     Biome::Forest},

    {"Turkey Tail", "mushroom", "Thin banded fan-shelves in rainbow stripes on logs.",
     "Too tough to eat -- simmered for tea or tincture, not chewed.",
     "Snap off firm, colorful shelves from dead hardwood; dry for tea.",
     MO(9) | MO(10) | MO(11) | MO(12) | MO(1), Biome::Forest},

    {"Artist's Conk", "mushroom",
     "Woody hoof-shaped bracket, white pore surface takes a scratch drawing.",
     "Too woody to eat fresh -- used dried for tea, not as food.",
     "Look for shelf brackets on standing or fallen conifers year-round.",
     MO(1) | MO(9) | MO(10) | MO(11) | MO(12), Biome::Forest},

    {"Chicken of the Woods", "mushroom",
     "Bright orange-yellow shelving on wounds of oak, conifer stumps.",
     "Cook thoroughly; some people react with GI upset, especially conifer-grown ones -- try a "
     "small amount first.",
     "Cut only the tender outer edge of a fresh shelf, leave the tough base.",
     MO(8) | MO(9) | MO(10), Biome::Forest},

    {"Hen of the Woods", "mushroom", "Ruffled grey-brown rosette at the base of old oaks.", "",
     "Check the base of mature oaks in the same spot every fall -- it returns for years.",
     MO(9) | MO(10), Biome::Forest},

    {"Shrimp Russula", "mushroom", "Reddish-pink cap, brittle white gills, mild in conifer duff.",
     "Russulas vary widely -- taste a tiny raw bit and spit it out; peppery ones are inedible.",
     "Look for brittle, chalky-snapping stems under Douglas fir.", MO(9) | MO(10), Biome::Forest},

    {"Cauliflower Coral", "mushroom", "Pale branching coral clusters at conifer bases.",
     "Distinguish from thin, brittle toxic corals -- this one is thick and fleshy.",
     "Cut the whole clump at the base; check for grubs in the crevices.", MO(9) | MO(10) | MO(11),
     Biome::Forest},

    {"Golden Chanterelle", "mushroom",
     "Deep egg-yolk color, wavy cap, distinct from the paler common chanterelle.",
     "False chanterelle (jack-o'-lantern) has true, sharp gills and glows faintly -- check for the "
     "blunt false ridges.",
     "Search mossy Douglas fir slopes a week after a warm rain.", MO(9) | MO(10), Biome::Forest},

    {"White Chanterelle", "mushroom",
     "Pale ivory cousin of the golden chanterelle, same false gills.", "",
     "Look in the same duff patches as goldens, slightly earlier in the season.", MO(8) | MO(9),
     Biome::Forest},

    {"Jack-o'-Lantern", "mushroom",
     "Bright orange clusters on buried roots, true sharp gills.",
     "Toxic -- causes severe vomiting; the classic chanterelle lookalike, ID by true blade-like "
     "gills.",
     "Do not pick -- note the clustered growth on wood, not soil, as a warning sign.",
     MO(9) | MO(10), Biome::Forest},

    {"Deadly Webcap", "mushroom",
     "Rusty-brown cap with a cobwebby veil, common in conifer duff.",
     "Deadly poisonous -- causes delayed, irreversible kidney failure; never eat any brown "
     "Cortinarius.",
     "Do not harvest -- the whole genus is best left alone by beginners.", MO(9) | MO(10) | MO(11),
     Biome::Forest},

    {"Angel Wings", "mushroom",
     "Small white shelving fungus on conifer logs, resembles oyster mushroom.",
     "Linked to rare fatal poisonings in susceptible people -- avoid entirely despite resembling "
     "oysters.",
     "Do not harvest -- if it's growing on conifer wood, it isn't the true oyster.",
     MO(10) | MO(11), Biome::Forest},

    {"Puffball (Giant)", "mushroom", "Basketball-sized white puffball in fields and forest edges.",
     "Slice in half first -- must be solid white inside with no gill outline or you may have a "
     "young amanita.",
     "Pick while still firm and pure white before it yellows and turns to spore dust.",
     MO(9) | MO(10), Biome::Forest},

    {"Black Trumpet", "mushroom",
     "Thin, funnel-shaped, nearly black -- 'trumpet of death' in name only.", "",
     "Search mossy hardwood-conifer mix slopes; they hide in shadow and leaf litter.",
     MO(9) | MO(10) | MO(11), Biome::Forest},

    {"Admirable Bolete", "mushroom", "Reddish-brown cap, yellow pores, firm flesh under conifers.",
     "Bruises blue when cut -- harmless, but confirm pore color stays yellow, not red-orange.",
     "Check firm, dry-capped boletes on well-drained forest slopes.", MO(9) | MO(10),
     Biome::Forest},

    {"Slippery Jack", "mushroom", "Sticky brown-capped bolete under pines, glue-like when wet.",
     "Peel the slimy cap skin -- it can upset sensitive stomachs.",
     "Look under planted pines; the slick cap is diagnostic.", MO(9) | MO(10) | MO(11),
     Biome::Forest},

    {"Angel's Wing Bolete", "mushroom",
     "Orange-brown scaly cap, yellow pores, grows under Douglas fir only.", "",
     "Search specifically under Douglas fir needles, its only host tree.", MO(9) | MO(10),
     Biome::Forest},

    {"Meadow Mushroom", "mushroom",
     "Wild cousin of the grocery button mushroom, in grassy clearings.",
     "Confirm pink-to-brown gills and no basal sac -- rules out deadly Amanita.",
     "Check the base for a volva sac before eating any lookalike field mushroom.", MO(9) | MO(10),
     Biome::Forest},

    {"Panther Cap", "mushroom",
     "Brown-capped amanita with white warts and a basal bulb.",
     "Toxic, causes neurological symptoms -- another reason to skip all warty amanitas.",
     "Do not harvest -- note the ring and bulb as amanita warning signs.", MO(9) | MO(10) | MO(11),
     Biome::Forest},

    {"Wood Blewit", "mushroom", "Lilac-tinted cap and gills, fruits late into cold weather.",
     "Must be cooked -- causes GI upset raw, and can resemble toxic Cortinarius; confirm the lilac "
     "gill color.",
     "Check leaf litter piles and compost edges after the first frosts.", MO(10) | MO(11) | MO(12),
     Biome::Forest},

    {"Indigo Milk Cap", "mushroom", "Slate-blue mushroom that bleeds indigo latex when cut.", "",
     "Slice the gills -- true blue milk oozing out confirms the ID.", MO(9) | MO(10),
     Biome::Forest},

    {"Old Man of the Woods", "mushroom",
     "Shaggy black-scaled bolete, easy to spot on the forest floor.", "",
     "Look for the distinctive shaggy black scales against pale flesh underneath.", MO(9) | MO(10),
     Biome::Forest},

    {"Witch's Butter", "mushroom",
     "Bright orange gelatinous blob on dead conifer branches after rain.", "",
     "Pick plump, jelly-firm blobs right after a soaking rain; they shrivel when dry.",
     MO(11) | MO(12) | MO(1) | MO(2), Biome::Forest},

    {"Oregon White Truffle", "mushroom",
     "Aromatic underground fungus near Douglas fir roots, found by scent or rake.", "",
     "Rake gently through duff near young Douglas fir where the soil smells earthy-ripe.",
     MO(10) | MO(11) | MO(12) | MO(1), Biome::Forest},

    {"Thimbleberry", "berry", "Maple-like leaf, soft red thimble-shaped fruit.", "",
     "Pick berries that crumble off the cap easily.", MO(7) | MO(8), Biome::Forest},

    {"Salal", "berry", "Evergreen leathery leaf, dark blue-black berry.", "",
     "Strip ripe dark berries off the flower spike.", MO(8) | MO(9), Biome::Forest},

    {"Red Huckleberry", "berry", "Bright red berry on angled green twigs on stumps.", "",
     "Check old nurse logs and stumps in shade.", MO(7) | MO(8), Biome::Forest},

    {"Blue Elderberry", "berry", "Powdery blue-black clusters on tall shrubs.",
     "Raw berries, seeds, leaves, and stems cause nausea -- cook and discard stems.",
     "Cut whole clusters, then cook before eating.", MO(8) | MO(9), Biome::Forest},

    {"Serviceberry", "berry", "Saskatoon. Sweet purple fruit in loose clusters.", "",
     "Strip ripe purple berries into a bag by hand.", MO(6) | MO(7), Biome::Forest},

    {"Kinnikinnick", "berry", "Bearberry. Mealy red fruit on trailing mats.",
     "Mealy and bland raw -- best cooked or dried, not a toxicity risk.",
     "Best simmered into syrup; raw fruit is dry.", MO(9) | MO(10) | MO(11), Biome::Forest},

    {"Trailing Blackberry", "berry", "Native bramble, low vines, smaller sweeter fruit.", "",
     "Search low along the ground, not tall canes.", MO(7) | MO(8), Biome::Forest},

    {"Indian Plum", "berry", "Earliest native bloom; bitter-to-sweet oval fruit.",
     "Seeds/pits contain cyanogenic compounds -- eat the flesh, not the pit.",
     "Wait for fruit to turn dark blue-black.", MO(6) | MO(7), Biome::Forest},

    {"Wild Strawberry", "berry", "Tiny intensely sweet fruit in forest openings.", "",
     "Search sunny forest-edge clearings and old trails.", MO(6) | MO(7), Biome::Forest},

    {"Bunchberry", "berry", "Dwarf dogwood, tight red berry cluster on the floor.",
     "Bland and seedy but not toxic -- mostly a trailside nibble.",
     "Look on mossy forest floor for the red cluster.", MO(8) | MO(9), Biome::Forest},

    {"Wine Cap Mushroom", "mushroom", "Burgundy cap fading tan, thick white ring, grows in wood-chip beds.",
     "No toxic lookalikes once the ring and chip habitat are confirmed.",
     "Check municipal wood-chip beds and garden mulch after rain.", MO(5) | MO(6) | MO(9) | MO(10), Biome::Forest},

    {"Sheep Sorrel", "green", "Arrow-shaped leaf, sharp lemony bite.",
     "High in oxalic acid -- a trailside nibble, not a meal.",
     "Pinch young leaves from sunny disturbed ground.", MO(4) | MO(5) | MO(6), Biome::Forest},

    {"Curly Dock", "green", "Wavy-edged dock leaf, tangy cooked green.",
     "High in oxalic acid; cook young leaves and eat in moderation.",
     "Take young spring leaves before they toughen.", MO(3) | MO(4), Biome::Forest},

    {"Bleeding Heart", "flower", "Rows of dangling pink heart-shaped flowers on an arching stem.",
     "Not edible -- mildly toxic; enjoy the look, skip the taste.",
     "Look for the pink heart blooms in shady forest clearings.", MO(4) | MO(5), Biome::Forest},

    {"Dandelion", "green", "Toothed leaf rosette, bitter green, yellow bloom.", "",
     "Pick young leaves before the flower stalk rises.", MO(2) | MO(3) | MO(4) | MO(5),
     Biome::Forest},

    {"Plantain", "green", "Ribbed oval leaf in every lawn and trail edge.", "",
     "Pick tender young leaves from unsprayed ground.", MO(5) | MO(6) | MO(7), Biome::Forest},

    {"Watercress", "green", "Peppery green mat rooted in cold running water.",
     "Harvest only from clean, fast-flowing water -- can carry liver fluke from livestock runoff.",
     "Gather from clean, fast-flowing streams only.", MO(4) | MO(5) | MO(10), Biome::Forest},

    {"Wild Mint", "green", "Square stem, minty scent, streamside patches.", "",
     "Crush a leaf to confirm the mint scent first.", MO(6) | MO(7) | MO(8), Biome::Forest},

    {"Self-heal", "flower", "Small purple flower spike in lawns and trailsides.", "",
     "Snip the flowering tops for tea or salad.", MO(6) | MO(7) | MO(8), Biome::Forest},

    {"Lupine", "flower", "Tall spike of pea-shaped blue-purple flowers on a leafy stalk.",
     "Seeds are mildly toxic in quantity -- admire the flower, skip eating any part.",
     "Look for the tall purple flower spikes in open meadows.", MO(6) | MO(7), Biome::Mountain},

    {"Glacier Lily", "flower", "Nodding yellow lily on a bare stalk, blooming right at snowmelt.",
     "The corm is edible cooked but digging it up wrecks the plant -- leave it for the marmots.",
     "Look for the reflexed yellow petals in fresh-melted alpine meadows.", MO(6) | MO(7), Biome::Mountain},

    {"Chaga", "mushroom", "Rough black charcoal-like burl growing straight out of birch bark.",
     "Not a typical mushroom -- a hardened fungal mass, brewed as tea rather than eaten.",
     "Look for the black clinker-like burl on live birch trunks.", MO(1) | MO(2) | MO(11) | MO(12), Biome::Forest},

    {"Lion's Mane", "mushroom", "Shaggy white pom-pom of dangling icicle spines, no cap or gills at all.",
     "",
     "Look for the toothed white ball on wounds in hardwood trunks.", MO(9) | MO(10) | MO(11),
     Biome::Forest},

    {"Saffron Milk Cap", "mushroom", "Orange cap that bleeds carrot-colored milk when cut, stains green with age.",
     "Bleeding orange/green milk is the easy tell -- few PNW lookalikes do this.",
     "Search under pine plantations after fall rain.", MO(9) | MO(10) | MO(11), Biome::Forest},

    {"Shaggy Parasol", "mushroom", "Large shaggy-scaled cap, ring on stem, browns when bruised.",
     "Confirm the ring and scaly cap -- a few Lepiota relatives are toxic.",
     "Look in grassy forest edges and clearings.", MO(8) | MO(9) | MO(10), Biome::Forest},

    {"Douglas Aster", "flower", "Lavender daisy-like blooms along forest edges and clearings in late summer.", "",
     "Pick the petals fresh; whole flowerheads are edible as a garnish.", MO(8) | MO(9) | MO(10), Biome::Forest},

    {"Beaked Hazelnut", "nut", "Native filbert in a bristly beaked husk.",
     "Husks have irritating fine bristles -- wear gloves when hulling.",
     "Gather husked nuts once they drop to the ground.", MO(8) | MO(9), Biome::Forest},

    {"Garry Oak Acorn", "nut", "Oak acorn needing leaching before eating.",
     "Raw acorns are bitter with tannins -- must be leached in water before eating.",
     "Shell, chop, and soak in changed water to leach tannin.", MO(9) | MO(10), Biome::Forest},

    {"Yellow Salsify", "green", "Grass-like leaves and a big dandelion-style seed puff; root and shoots both edible.", "",
     "Young rosettes are best before the yellow flower opens.", MO(5) | MO(6) | MO(7), Biome::Forest},

    {"Cottonwood Buds", "bud", "Resinous balm-of-Gilead bud, sweet balsam scent.",
     "Sticky resin can irritate sensitive skin -- for salves, not raw eating.",
     "Pinch sticky buds before leaves unfurl for salve.", MO(1) | MO(2) | MO(3), Biome::Forest},

    {"Oxeye Daisy", "green", "White-petaled daisy, edible bitter young leaf.", "",
     "Pick basal leaves before the flower stalk bolts.", MO(4) | MO(5), Biome::Forest},

    {"Wax Currant", "berry", "Tart orange-red berries on dry, rocky mountain slopes.", "",
     "Pick plump translucent berries; sticky sap on the bush is normal.", MO(7) | MO(8),
     Biome::Mountain},

    {"Red-Flowering Currant", "berry", "Bland blue-black fruit follows the pink spring bloom.", "",
     "Best cooked into jam -- raw berries are mealy and mild.", MO(7) | MO(8), Biome::Mountain},

    {"Oregon Grape", "berry", "Holly-like leaves, sour blue berries for jelly.",
     "Very tart and seedy raw -- best cooked and strained.",
     "Strip clusters once berries turn deep dusty blue.", MO(8) | MO(9), Biome::Mountain},

    {"King Bolete Button", "mushroom", "Young unopened Boletus edulis, firm white pores, before the cap flattens.",
     "No toxic boletes with the classic white-pore, non-bruising profile at this stage.",
     "Check conifer duff a few days after warm rain.", MO(8) | MO(9) | MO(10), Biome::Mountain},

    {"Alpine Blueberry", "berry", "Low sprawling shrub with powdery blue berries just above treeline.", "",
     "Best right where the shrub barely clears the ground near rock fields.", MO(8) | MO(9), Biome::Mountain},

    {"Subalpine Daisy", "flower", "Lavender-rayed daisy with a yellow center, carpeting subalpine meadows.", "",
     "Petals make a mild garnish; pick from large stands only.", MO(7) | MO(8), Biome::Mountain},

    {"Labrador Tea", "green", "Fuzzy-backed leaves in subalpine bogs, brewed as tea.",
     "Contains toxic compounds in quantity -- steep weak, small amounts only, skip if pregnant.",
     "Pick a few leathery leaves, dry them before brewing.", MO(6) | MO(7) | MO(8),
     Biome::Mountain},

    {"Yarrow", "flower", "Feathery leaves, flat white flower heads in dry meadows.",
     "Mild in tea, but can irritate skin or upset stomach in large doses.",
     "Snip flower heads in full bloom; leaves work fresh or dried.", MO(6) | MO(7) | MO(8),
     Biome::Mountain},

    {"Indian Rhubarb", "green", "Umbrella-leaf plant along mountain streambanks.",
     "High in oxalic acid -- a trailside nibble, not a meal.",
     "Peel young stalks before the leaf fully unfurls; cook like rhubarb.", MO(5) | MO(6),
     Biome::Mountain},

    {"Hawk's Wing", "mushroom", "Scaly cap, toothed underside, in conifer duff.",
     "Teeth instead of gills make ID easy; older caps turn bitter -- pick young.",
     "Look on mossy conifer slopes; younger, paler specimens taste best.", MO(9) | MO(10),
     Biome::Mountain},

    {"Bear's Head Tooth", "mushroom", "Cascading white icicle spines on conifer logs.",
     "No toxic lookalikes -- shape and spines make ID easy.",
     "Check dead or dying conifer trunks and stumps at mid-elevation.", MO(9) | MO(10),
     Biome::Mountain},

    {"Alpine Strawberry", "berry", "Tiny intensely sweet strawberries tucked in rocky subalpine turf.", "",
     "Look low to the ground in sunny rocky openings.", MO(7) | MO(8), Biome::Mountain},

    {"Red Currant", "berry", "Translucent red berry clusters dangling from an arching mountain shrub.", "",
     "Strip whole clusters once berries turn glassy red.", MO(7) | MO(8), Biome::Mountain},

    {"Grouse Whortleberry", "berry", "Pea-sized red berries carpeting ground right at treeline.",
     "", "Comb low mats with fingers -- tedious, but the berries are intensely sweet.",
     MO(8) | MO(9), Biome::Mountain},

    {"Black Raspberry", "berry", "Blackcap. Purple-black cap pulls free of a dry cup.", "",
     "Found in mountain clearcuts and burns; ripe caps detach clean, leaving the core behind.",
     MO(7) | MO(8), Biome::Mountain},

    {"Twisted Stalk", "berry", "Watermelon berry. Red drops hang singly under the leaves.",
     "Mildly laxative in quantity -- a trailside treat, not a basketful.",
     "Check under the zigzag stem in moist subalpine forest for single hanging berries.",
     MO(8) | MO(9), Biome::Mountain},

    {"Soapberry", "berry", "Bitter red berries traditionally whipped into a froth.",
     "Sharp, bitter raw and mildly upsetting in quantity -- best whipped and sweetened.",
     "Strip clusters off dry eastside mountain shrubs after they turn translucent red.",
     MO(8) | MO(9), Biome::Mountain},

    {"Whitebark Pine Nuts", "pine nut", "Fat, buttery seed from a threatened high-elevation pine.",
     "Endangered tree -- gather only from fallen cones, never harm live trees.",
     "Look for cones already dropped below snags near ridgelines.", MO(8) | MO(9), Biome::Mountain},

    {"Western White Pine Nuts", "pine nut",
     "Long cones with small, sweet seeds tucked under each scale.", "",
     "Collect fresh-fallen cones and pry the scales open for seeds.", MO(9) | MO(10),
     Biome::Mountain},

    {"Licorice Fern", "fern", "Slender fern growing straight out of mossy maple trunks and logs.", "",
     "Look for green fronds sprouting from thick moss on bigleaf maple.", MO(10) | MO(11) | MO(1),
     Biome::Forest},

    {"Subalpine Fir Tips", "tree tip", "Balsam-scented new growth right at the treeline.",
     "Don't confuse with Pacific yew -- yew needles are toxic.",
     "Pinch pale new candle growth from lower, reachable branches.", MO(5) | MO(6),
     Biome::Mountain},

    {"Grand Fir Tips", "tree tip", "Glossy needles with a bright orange-citrus scent when crushed.",
     "Don't confuse with Pacific yew -- yew needles are toxic.",
     "Take a few soft new tips per branch and leave the rest.", MO(4) | MO(5), Biome::Mountain},

    {"Wild Gooseberry", "berry", "Spiny stems, dangling purple-veined berries in damp mountain draws.",
     "Skip the spiny stem -- fruit itself has no toxic lookalike.",
     "Reach past the spines to strip ripe berries into a container.", MO(7) | MO(8), Biome::Mountain},

    {"Highbush Cranberry", "berry", "Translucent red berry clusters dangling from a maple-like shrub.", "",
     "Look for grape-like clusters along stream edges in fall.", MO(9) | MO(10), Biome::Forest},

    {"Black Huckleberry", "berry", "Deep purple-black berries on a mid-elevation shrub, the classic PNW huckleberry.", "",
     "Best in burn sites and open subalpine slopes.", MO(8) | MO(9), Biome::Mountain},

    {"Mountain Sorrel Leaves", "green", "Small kidney-shaped leaves with a sharp lemony bite, tucked in rocky seeps.", "",
     "Pick a few young leaves per plant from rocky wet crevices.", MO(6) | MO(7) | MO(8), Biome::Mountain},

    {"Subalpine Fireweed", "flower", "Tall pink-purple spikes colonizing high slopes after snowmelt or fire.", "",
     "Pick individual flowers as they open up the spike.", MO(7) | MO(8), Biome::Mountain},

    {"Wild Blueberry", "berry", "Tiny tart blueberries on ankle-high subalpine mats.", "",
     "Comb low mats in open sun near the treeline.", MO(8) | MO(9), Biome::Mountain},

    {"Snowberry", "berry", "Clusters of bright white berries on arching stems in forest understory.",
     "Not edible -- mildly toxic (saponins); enjoy the look, skip the taste.",
     "Look for the ghostly white berry clusters through fall and winter.", MO(9) | MO(10) | MO(11),
     Biome::Forest},

    {"Pearly Everlasting", "herb", "Papery white everlasting bloom, dried for a mild herbal tea.",
     "", "Cut flowering stalks and hang them to dry before storing.", MO(7) | MO(8) | MO(9),
     Biome::Mountain},

    {"Nootka Rose", "flower", "Fragrant single pink five-petaled wild rose on a thorny bush.", "",
     "Look for the bright pink open blooms along trail edges.", MO(5) | MO(6),
     Biome::Mountain},

    {"Fireweed Shoots", "shoot", "Asparagus-like spring shoot from the tall pink-flowered burns.",
     "", "Snap tender shoots under 8 inches before they toughen.", MO(4) | MO(5), Biome::Mountain},

    {"Juniper Berries", "berry", "Blue-black cone scale used whole as a savory mountain spice.",
     "Confirm true common juniper -- don't confuse with toxic yew berries nearby.",
     "Pick fully blue-black cones and skip any still green.", MO(9) | MO(10) | MO(11),
     Biome::Mountain},

    {"Mountain Ash Berries", "berry",
     "Orange berry cluster on subalpine shrubs, bitter until cooked.",
     "Mildly toxic raw -- cook or freeze before eating any quantity.",
     "Pick after frost, then cook; raw berries upset the stomach.", MO(9) | MO(10),
     Biome::Mountain},

    {"Red Elderberry", "berry",
     "Red berry cluster by mountain streams, riskier than blue elderberry.",
     "Raw berries, seeds, and stems are toxic -- must be cooked and strained.",
     "Cook thoroughly and strain out seeds; never eat raw.", MO(6) | MO(7), Biome::Mountain},

    {"Pipsissewa", "herb", "Waxy evergreen leaf whorl used to flavor a traditional root tea.", "",
     "Snip a few leathery leaves per plant from the shaded forest floor.",
     MO(6) | MO(7) | MO(8) | MO(9), Biome::Mountain},

    {"Nori (Laver)", "seaweed", "Purple-black sheets on rocks. Dries paper-thin in sun.", "",
     "Peel thin sheets off high rocks at the lowest winter tides.",
     MO(10) | MO(11) | MO(12) | MO(1) | MO(2) | MO(3), Biome::Coast},

    {"Bladderwrack", "seaweed", "Forked brown fronds with paired air bladders.", "",
     "Snip fronds above the holdfast; the bladders pop when ripe.",
     MO(4) | MO(5) | MO(6) | MO(7) | MO(8), Biome::Coast},

    {"Winged Kelp", "seaweed", "Long brown blade with a pale edible midrib.",
     "Strip the tough wing from the midrib before eating.",
     "Cut young blades before the midrib turns fibrous.", MO(5) | MO(6) | MO(7) | MO(8),
     Biome::Coast},

    {"Sea Palm", "seaweed", "Palm-like stipe braced in the crashing surf zone.",
     "Grows only where waves are heaviest -- footing is the real risk.",
     "Cut a few fronds per holdfast so the cluster regrows.", MO(6) | MO(7) | MO(8), Biome::Coast},

    {"Feather Boa Kelp", "seaweed", "Long feathered blade strand, chewy and briny.", "",
     "Gather fresh drift strands rather than tearing live fronds.", MO(6) | MO(7) | MO(8) | MO(9),
     Biome::Coast},

    {"Turkish Towel", "seaweed", "Thick rubbery red blade, rough like a washcloth.", "",
     "Peel whole blades from low rocks at a minus tide.", MO(6) | MO(7) | MO(8) | MO(9),
     Biome::Coast},

    {"Turkish Washcloth", "seaweed", "Dark curled red-black blades, papery when dry.", "",
     "Pinch fronds above the holdfast on mid-tide rocks.", MO(4) | MO(5) | MO(6) | MO(7) | MO(8),
     Biome::Coast},

    {"Sea Sac", "seaweed", "Golf-ball brown blobs stuck fast to low rocks.", "",
     "Twist whole sacs free at the lowest summer tides.", MO(6) | MO(7) | MO(8), Biome::Coast},

    {"Oarweed", "seaweed", "Broad divided blade, thick rubbery stipe, low rocky shore.", "",
     "Cut blades above the holdfast at a low tide, leaving it rooted.",
     MO(5) | MO(6) | MO(7) | MO(8), Biome::Coast},

    {"Sea Cabbage", "seaweed", "Ruffled golden blade, milder cousin of sugar kelp.", "",
     "Cut blades an inch above the holdfast at low tide.", MO(4) | MO(5) | MO(6) | MO(7),
     Biome::Coast},

    {"Sea Hair", "seaweed", "Hollow bright-green tubes tangled on tidepool rocks.",
     "Rinse thoroughly -- traps fine sand inside the tube.",
     "Pull loose green tangles from mid-tide rocks and pools.", MO(4) | MO(5) | MO(6) | MO(7),
     Biome::Coast},

    {"Giant Kelp", "seaweed", "Towering brown kelp forest off the open coast.", "",
     "Gather fresh blades adrift after a swell, not the holdfast.",
     MO(6) | MO(7) | MO(8) | MO(9) | MO(10), Biome::Coast},

    {"Beach Sandwort", "green", "Succulent dune leaves in low mats above the tideline.", "",
     "Pinch tender tips before the plant flowers and toughens.", MO(4) | MO(5) | MO(6),
     Biome::Coast},

    {"American Searocket", "green", "Fleshy dune plant, peppery like arugula.", "",
     "Pick young leaves and green pods before they woodify.", MO(6) | MO(7) | MO(8) | MO(9),
     Biome::Coast},

    {"Orache", "green", "Silvery-green spinach relative on the upper beach.", "",
     "Snip young top leaves before the seed heads form.", MO(5) | MO(6) | MO(7) | MO(8),
     Biome::Coast},

    {"Scurvy Grass", "green", "Small round leaves, peppery like watercress.", "",
     "Pick tender rosettes from rocky splash-zone crevices.", MO(3) | MO(4) | MO(5), Biome::Coast},

    {"Sea Coast Angelica", "green", "Celery-scented stalks in coastal meadows and bluffs.",
     "Apiaceae family -- confirm ID carefully, hemlock lookalikes kill.",
     "Peel young spring stalks before the flower stem hardens.", MO(4) | MO(5) | MO(6),
     Biome::Coast},

    {"Beach Lovage", "green", "Wild celery leaf, glossy and salty-sweet.",
     "Apiaceae family -- confirm ID carefully, hemlock lookalikes kill.",
     "Snip young leaves from low bluff-top patches in spring.", MO(4) | MO(5) | MO(6),
     Biome::Coast},

    {"Pacific Oyster", "shellfish", "Rock-cemented bivalve on sheltered tideflat beaches.",
     "Check PSP/biotoxin closures before eating any raw shellfish.",
     "Pry from rock clusters at a minus tide, shuck fresh.",
     MO(9) | MO(10) | MO(11) | MO(12) | MO(1) | MO(2) | MO(3) | MO(4), Biome::Coast},

    {"Bay Mussel", "shellfish", "Blue-black shells clustered on pilings and rocks.",
     "Avoid summer months -- biotoxin quarantines run roughly Jul-Oct.",
     "Twist clusters free from rocks at the lowest tides.",
     MO(11) | MO(12) | MO(1) | MO(2) | MO(3) | MO(4) | MO(5) | MO(6), Biome::Coast},

    {"Butter Clam", "shellfish", "Deep-digging clam, thick chalky-white shell.",
     "Holds PSP toxin longest of any local clam -- check closures.",
     "Dig a foot down in firm sand-gravel beaches.",
     MO(10) | MO(11) | MO(12) | MO(1) | MO(2) | MO(3), Biome::Coast},

    {"Geoduck", "shellfish", "Giant burrowing clam with a long siphon neck.",
     "Check state biotoxin closures and permit rules before digging.",
     "Follow the siphon 'show' straight down with a tube and shovel.",
     MO(10) | MO(11) | MO(12) | MO(1) | MO(2) | MO(3) | MO(4), Biome::Coast},

    {"Gooseneck Barnacle", "shellfish", "Leathery stalked barnacle clumped on surf-battered rock.",
     "Harvest only where locally legal -- some areas restrict picking.",
     "Twist clusters from wave-exposed rock at the lowest tides.", MO(3) | MO(4) | MO(5) | MO(6),
     Biome::Coast},

    {"Dungeness Crab", "shellfish", "Iconic sweet-meat crab of eelgrass and sandy flats.",
     "Check size, sex, and season limits before keeping any crab.",
     "Set rings baited with fish near eelgrass at high tide.",
     MO(7) | MO(8) | MO(9) | MO(10) | MO(11) | MO(12), Biome::Coast},

    {"Red Rock Crab", "shellfish", "Smaller, chunky-clawed crab under low-tide rocks.",
     "Check size and daily limits before keeping any crab.",
     "Flip low-tide rocks and boulders to find them hiding.",
     MO(4) | MO(5) | MO(6) | MO(7) | MO(8) | MO(9), Biome::Coast},

    {"Black Katy Chiton", "shellfish", "Leathery black armor-plated grazer on open rock.",
     "Tough and strong-flavored -- tenderize well before eating.",
     "Pry gently from open rock faces at the lowest tides.", MO(4) | MO(5) | MO(6) | MO(7) | MO(8),
     Biome::Coast},

    {"Red Sea Urchin", "shellfish", "Long-spined purple-red urchin, prized for its roe.",
     "Handle spines with care; roe quality varies by season.",
     "Look in subtidal rock crevices at the lowest minus tides.", MO(5) | MO(6) | MO(7) | MO(8),
     Biome::Coast},

    {"Limpet", "shellfish", "Cone-shelled grazer clamped tight to open rock.", "",
     "Pop them loose fast with a knife before they clamp down.",
     MO(4) | MO(5) | MO(6) | MO(7) | MO(8), Biome::Coast},

    {"Pacific Basket Cockle", "shellfish", "Ribbed round shell resting just under sandy gravel.",
     "Check state biotoxin/PSP closures before digging.",
     "Rake shallow sand-gravel flats a few inches down.",
     MO(10) | MO(11) | MO(12) | MO(1) | MO(2) | MO(3), Biome::Coast},

    {"Nudibranch", "shellfish", "Wildly colorful sea slug with feathery gills, crawling on tidepool rock.",
     "Not edible -- toxic defenses borrowed from its prey.",
     "Look in tidepools and subtidal rock at the lowest minus tides.", MO(5) | MO(6) | MO(7) | MO(8),
     Biome::Coast},

    {"Moon Snail", "shellfish", "Large round predator snail plowing through tide-flat sand.",
     "Tough meat needs long tenderizing -- an acquired harvest.",
     "Follow its smooth plow-trail across exposed sand flats.", MO(5) | MO(6) | MO(7) | MO(8),
     Biome::Coast},

    {"Purple Varnish Clam", "shellfish", "Shiny purple-brown shell, shallow in sandy beaches.",
     "Check state biotoxin/PSP closures before digging.",
     "Rake the top few inches of sand at any minus tide.",
     MO(3) | MO(4) | MO(5) | MO(6) | MO(7) | MO(8) | MO(9) | MO(10), Biome::Coast},

    {"Manila Clam", "shellfish", "Ridged shell, common on protected bay tideflats.",
     "Check state shellfish biotoxin closures before digging.",
     "Dig 6-8 inches down at low tide with a rake or fork.",
     MO(10) | MO(11) | MO(12) | MO(1) | MO(2) | MO(3) | MO(4), Biome::Coast},

    {"Pacific Littleneck Clam", "shellfish", "Native littleneck, deeper-ridged than the Manila.",
     "Check state shellfish biotoxin closures before digging.",
     "Found a bit deeper than Manila clams in gravelly sand.",
     MO(10) | MO(11) | MO(12) | MO(1) | MO(2) | MO(3) | MO(4), Biome::Coast},

    {"Pacific Gaper Clam", "shellfish", "Big clam, siphon too large to fully retract.",
     "Trim and discard the dark rubbery siphon skin before eating.",
     "Look for a squirting hole in sand at an extreme low tide.",
     MO(10) | MO(11) | MO(12) | MO(1) | MO(2) | MO(3), Biome::Coast},

    {"Softshell Clam", "shellfish", "Thin brittle shell common in estuary mudflats.", "",
     "Dig soft mud near creek mouths; the shell breaks easily.",
     MO(9) | MO(10) | MO(11) | MO(12) | MO(1) | MO(2) | MO(3), Biome::Coast},

    {"California Mussel", "shellfish", "Large ridged mussel on wave-battered outer rocks.",
     "Skip harvest in warm months when biotoxin risk peaks.",
     "Pry from exposed surf rocks only on a good minus tide.",
     MO(9) | MO(10) | MO(11) | MO(12) | MO(1) | MO(2) | MO(3) | MO(4), Biome::Coast},

    {"Olympia Oyster", "shellfish", "Tiny native oyster, coin-sized and slow-growing.",
     "Native beds are limited -- take only where restoration allows.",
     "Look on quiet bay shell substrate below the mussel line.",
     MO(9) | MO(10) | MO(11) | MO(12) | MO(1) | MO(2) | MO(3) | MO(4), Biome::Coast},

    {"Kelp Crab", "crab", "Olive, spider-legged crab living in kelp beds.", "",
     "Hand-pick from kelp holdfasts at a low tide.", MO(6) | MO(7) | MO(8) | MO(9), Biome::Coast},

    {"Graceful Crab", "crab", "Smaller cousin of Dungeness, a common bycatch.", "",
     "Found in the same pots and pools as Dungeness crab.", MO(7) | MO(8) | MO(9), Biome::Coast},

    {"Purple Sea Urchin", "urchin", "Spiny purple test; the roe is the harvested part.",
     "Handle spines with gloves; check season and daily limits.",
     "Pry loose from low rocky tidepools at a minus tide.",
     MO(10) | MO(11) | MO(12) | MO(1) | MO(2) | MO(3), Biome::Coast},

    {"Gumboot Chiton", "chiton", "Football-sized, rust-red 'wandering meatloaf.'",
     "Take only the muscular foot; harvest sparingly, population-sensitive.",
     "Pry gently from rock faces on the lowest spring tides.", MO(4) | MO(5) | MO(6) | MO(7),
     Biome::Coast},

    {"Blue Top Snail", "snail", "Small conical shell grazing low tidepool rocks.", "",
     "Hand-pick from tidepools; boil briefly to free the foot.",
     MO(4) | MO(5) | MO(6) | MO(7) | MO(8) | MO(9), Biome::Coast},

    {"Spot Prawn", "shrimp", "Sweet pink shrimp with a very short spring season.",
     "WA's recreational season is brief -- confirm exact open dates.",
     "Drop baited pots into deep water off the outer coast.", MO(5), Biome::Coast},

    {"Pinto Abalone", "shellfish", "Ear-shaped shell snail, now critically depleted.",
     "Harvest is illegal in WA waters -- look, photograph, don't take.",
     "Spot clinging to subtidal rock; leave every one in place.",
     MO(4) | MO(5) | MO(6) | MO(7) | MO(8) | MO(9), Biome::Coast},

    {"Evergreen Huckleberry", "berry", "Glossy coastal shrub, small dark berries into winter.", "",
     "Comb dense coastal understory shrubs after other berries fade.",
     MO(9) | MO(10) | MO(11) | MO(12), Biome::Coast},

    {"Partridgefoot Greens", "green", "Mossy mat of tiny fan-shaped leaves and white flower spikes on coastal bluffs.", "",
     "Snip a few leaf tufts from large, well-established mats.", MO(6) | MO(7), Biome::Coast},

    {"Gem-Studded Puffball", "mushroom", "Warty white ball in duff; cut in half to check.",
     "Interior must be pure white throughout -- yellow or gill shadow means don't eat.",
     "Pick young, before the skin yellows or splits.", MO(9) | MO(10) | MO(11), Biome::Forest},

    {"Pigskin Poison Puffball", "mushroom",
     "Thick, scaly rind and black marbled inside -- not edible.",
     "Toxic -- dark purple-black interior distinguishes it from true puffballs, which are pure "
     "white.",
     "Learn to recognize and leave it; it's a common lookalike hazard.", MO(9) | MO(10) | MO(11),
     Biome::Forest},

    {"Zeller's Bolete", "mushroom", "Dark maroon cap, yellow pores, blue bruise. Under conifers.",
     "Confirm pores bruise blue, not red; avoid soft or slimy caps.",
     "Firm caps only, cut base to check for tunneling grubs.", MO(9) | MO(10) | MO(11),
     Biome::Forest},

    {"Butter Bolete", "mushroom", "Smooth tan cap, thick stem, mild buttery flavor.",
     "Check pore color is pale yellow, not orange-red, before eating.",
     "Look on mossy ground under hemlock after fall rain.", MO(10) | MO(11), Biome::Forest},

    {"Pig's Ears", "mushroom", "Purple-brown, vase-shaped chanterelle relative in mossy duff.",
     "False gills like a chanterelle, not true blades -- safe ID feature.",
     "Look near hemlock roots where moss stays damp.", MO(9) | MO(10), Biome::Forest},

    {"Woolly Chanterelle", "mushroom", "Shaggy orange funnel, showy but upsets stomachs raw.",
     "Causes GI upset for many people -- cook thoroughly and try a small amount first.",
     "Easy to spot by its ragged, scaly orange cap.", MO(9) | MO(10), Biome::Forest},

    {"Coral Tooth Fungus", "mushroom",
     "Branching white coral studded with tiny icicle teeth on wounds in bigleaf maple.",
     "Distinguish by branching form from unbranched Bear's Head on the same logs.",
     "Cut the whole cluster where it grows from a wound scar.", MO(9) | MO(10) | MO(11),
     Biome::Forest},

    {"Wood Ear", "mushroom", "Rubbery brown ear-shaped shelves on dead alder and elder branches.",
     "No toxic lookalikes in the region, but cook thoroughly before eating.",
     "Pull whole cup-shaped clusters off the bark; dries well for storage.",
     MO(1) | MO(10) | MO(11) | MO(12), Biome::Forest},

    {"Amber Jelly Roll", "mushroom", "Small amber jelly blobs on dead willow and alder twigs.",
     "Not toxic, but flavorless -- mostly a winter curiosity, not a meal.",
     "Look after freeze-thaw cycles swell the jelly back up.", MO(1) | MO(11) | MO(12),
     Biome::Forest},

    {"Black Witch's Butter", "mushroom", "Dark olive-black jelly lumps on dead hardwood branches.",
     "Edible but rubbery and bland -- best simmered into broths, not eaten raw.",
     "Rehydrates from a shriveled black crust after rain -- pick it plump.",
     MO(1) | MO(11) | MO(12), Biome::Forest},

    {"Cinnabar Polypore", "mushroom",
     "Bright orange-red bracket fungus fused flat to dead hardwood.",
     "Too tough and woody to eat -- valued for its dye, not the table.",
     "Pry brackets whole off the log; the color persists when dried.",
     MO(9) | MO(10) | MO(11) | MO(12), Biome::Forest},

    {"Orange Peel Fungus", "mushroom",
     "Bright orange cup fungus scattered on bare, disturbed soil.",
     "Edible raw, but confirm the bright orange upper surface and pale underside.",
     "Look along gravel paths and disturbed forest edges after rain.", MO(9) | MO(10) | MO(11),
     Biome::Forest},

    {"Fried Chicken Mushroom", "mushroom",
     "Dense gray-brown clusters at the base of hardwoods, smells savory.",
     "Cook thoroughly; some people react to it raw or undercooked.",
     "Cut whole tight clusters at the stem base near the trunk.", MO(9) | MO(10) | MO(11),
     Biome::Forest},

    {"Honey Mushroom", "mushroom",
     "Honey-gold caps in dense clusters at stump bases, black shoestrings beneath bark.",
     "Must be cooked thoroughly; confirm the black rhizomorph threads under bark to rule out "
     "deadly Galerina.",
     "Twist clusters free at the stump; check for the telltale ring on the stem.",
     MO(9) | MO(10) | MO(11), Biome::Forest},

    {"Snow Bank False Morel", "mushroom",
     "Reddish-brown brain-like cap pushing up at the edge of melting snow.",
     "Toxic raw and even parboiled for some people -- true morels are hollow, this one is "
     "chambered, not worth the risk.",
     "Best left alone; note it only to avoid confusing it with true morels.", MO(4) | MO(5),
     Biome::Forest},

    {"Blue Chanterelle", "mushroom", "Small violet-blue funnel, false gills, in deep conifer duff.",
     "False ridges like true chanterelles; color alone confirms it's not a lookalike.",
     "Easy to miss against blue-shadowed duff -- look closely, not just for orange.",
     MO(9) | MO(10), Biome::Forest},

    {"Birch Polypore", "mushroom", "Smooth pale-brown kidney-shaped bracket found only on birch.", "",
     "Pick young, still-flexible brackets low on birch trunks.", MO(8) | MO(9) | MO(10), Biome::Forest},

    {"Dryad's Saddle", "mushroom", "Big scaly tan bracket smelling of watermelon rind, on hardwood wounds.",
     "Pick only young, still-tender brackets -- older ones turn woody, not toxic just inedible.",
     "Check fresh wounds and stumps on maple and cottonwood each spring.", MO(4) | MO(5) | MO(6), Biome::Forest},

    {"Sword Fern", "fern", "Evergreen forest fern; rhizome was an emergency staple.",
     "Rhizome is bitter and fibrous -- historically peeled, roasted, and used mainly in famine "
     "years.",
     "Dig only a rhizome section from an abundant patch, leave the crown.",
     MO(1) | MO(2) | MO(3) | MO(10) | MO(11) | MO(12), Biome::Forest},

    {"Deer Fern Fiddlehead", "fern", "Low, glossy forest fern with slender upright fronds.",
     "Eat only young coiled fiddleheads, cooked; raw fronds are tough and gritty.",
     "Snap coiled fronds where they bend easily, leave most per plant.", MO(4) | MO(5),
     Biome::Forest},

    {"Vanilla Leaf", "green", "Fan of three broad leaflets carpeting the forest floor, vanilla scent when dried.", "",
     "Look for the distinctive three-lobed fan leaf low in shady forest.", MO(4) | MO(5),
     Biome::Forest},

    {"Lady Fern Fiddlehead", "fern", "Lacy-fronded fern of moist forest floors and streambanks.",
     "Cook thoroughly; discard the papery brown scales before eating.",
     "Pick coils under 6 inches, tightly furled, from healthy clumps.", MO(4) | MO(5),
     Biome::Forest},

    {"Cattail Shoots", "green", "Tall marsh reed; peeled inner core tastes like cucumber.",
     "Confirm the flat, strap-like leaves -- avoid marsh areas with runoff contamination.",
     "Pull the young shoot and peel down to the tender white core.", MO(4) | MO(5) | MO(6),
     Biome::Forest},

    {"Skunk Cabbage", "flower", "Huge bright yellow hooded spathe pushing up through spring swamp mud.",
     "Raw leaves burn from calcium oxalate -- needs thorough drying/cooking, best left alone.",
     "Look for the glowing yellow hood in wet forest seeps.", MO(3) | MO(4), Biome::Forest},

};
