mrrosoff/Forager/src/foraging/foraging.h

// foraging.h — PNW / Seattle foraging calendar and species reference.
#pragma once

#include "model.h"

namespace foraging {

// month: 1..12. Returns the primary featured forageable for that month.
Forageable featured(int month);

// Returns the secondary forageable for that month.
Forageable secondary(int month);

// A short human-readable season note for the month (e.g. "Spring greens").
const char* seasonNote(int month);

// Master species reference list, for the browsable foraging menu.
int speciesCount();
const Forageable& speciesAt(int index);

// Rebuilds the Foraging view's browse order: relevance-ranked (in-season
// species first, a rain bonus for mushrooms) with per-wake randomization so
// it's not the same order every time. Call once per wake, before browsing.
// Only includes discovered species (see journal::isDiscovered()) -- the
// full reference isn't handed over on day one, see events::EventType::Discovery.
void rebuildBrowseOrder(int month, bool postRain);

// Number of discovered/browsable species, 0..speciesCount(). May be 0
// early on, before any Discovery encounters have resolved.
int browsableCount();

// Species at a browse-order rank (0..speciesCount()-1), after
// rebuildBrowseOrder(). Distinct from speciesAt(), which is raw array order
// (used by the random-pick ForagingFind event spawn).
const Forageable& speciesAtRank(int rank);

// The raw speciesAt()-style index backing a given rank -- lets callers
// (e.g. journal::markEaten()) resolve "the species currently on screen" to
// a stable index without depending on the browse-order internals directly.
int indexAtRank(int rank);

/**
 * Counts species of the given kind (e.g. "mushroom") already marked eaten
 * in journal::hasEaten() -- for the Achievements view's kind-based badges.
 */
int countEatenOfKind(const char* kind);

/**
 * Counts species of the given biome already marked eaten in
 * journal::hasEaten() -- for the Achievements view's biome-based badges.
 */
int countEatenOfBiome(Biome b);

// True if this species is in season for the given month (1..12).
bool inSeason(const Forageable& f, int month);

// Short label for a biome, e.g. "Coast" -- for display in the browsable menu.
const char* biomeName(Biome b);

}  // namespace foraging
